DankFlumeMister/StarShield/docs/decision-package-2026-09-18.md

# 待决策项决策包（2026-09-18）

> 本文件把 `docs/decisions.md`「待定」清单里的 **9 项**逐项推进到可决策状态：
> **现状 → 事实依据 → 选项 → 推荐 → 代价 → 待你拍板**。
> 已经能定案的项（P12、P15）已直接落地并同步到原理图与文档；其余项需要你确认后我再动手改。

## 0. 总览

| # | 项 | 类型 | 状态 | 我的推荐 | 需要你拍板 |
| --- | --- | --- | --- | --- | --- |
| 1 | **P12** `ZMK_RGB_UNDERGLOW_EXT_POWER` | 固件 | ✅ **已关闭** | —（早已开启） | 否 |
| 2 | **P15** `F1` 保险丝额定值 | 硬件 | ✅ **已定案并落地** | 2 A hold / 1812 PTC | 否（已知会你） |
| 3 | **G2** PCB 板框外扩量 | 结构 | ✅ **已确认（2026-09-18）** | 4 mm/边 ⇒ PCB 约 379 × 127 mm | 否 |
| 4 | **G3** 安装孔数量与位置 | 结构 | 🟡 部分可定 | 数量 **8 个 / M2** 已定；**坐标留到 B4** | 否（坐标在 B4 定） |
| 5 | **G4** 外壳分件方案 | 结构 | ✅ **用户自理（2026-09-18）** | 本项目只产出 3D 模型文件 | 否 |
| 6 | **G6** 定位板是否纳入第一版 | 结构 | ✅ **已确认（2026-09-18）** | **纳入** | 否 |
| 7 | **C4** 是否引入 ZMK Studio | 固件 | ✅ **已确认（2026-09-18）：暂不启用** | 物理布局已存在，将来启用只差两行配置 | 否 |
| 8 | **C6** 是否并行做树莓派 MIT 验证 | 固件 | ✅ **已确认（2026-09-18）：不做** | 成本太高；兼容性风险改由 C5 直接实测承接（建议先买 ESP32-S3 最小系统板） | 否 |
| 9 | **ZMK config 是否独立仓库** | 仓库 | ✅ **已确认（2026-09-18）** | **不拆** | 否 |

---

## 1. P12 —— `ZMK_RGB_UNDERGLOW_EXT_POWER` ✅ 已关闭（文档滞后，不是没做）

**现状**：`firmware/boards/shields/starshield/starshield.conf` **第 31 行已是**
`CONFIG_ZMK_RGB_UNDERGLOW_EXT_POWER=y`，其前置 `CONFIG_ZMK_EXT_POWER=y` 也在（第 47 行）。

**结论**：这一项**早已落地**，挂在待定清单里是文档没同步。语义正是我们想要的
（RGB 开关联动 `ext-power`，关灯时经 Q1/Q2 反相级**物理切断** LED 供电，见 ADR-0005）。
已在 `decisions.md` 标为已关闭。

---

## 2. P15 —— `F1` 保险丝额定值 ✅ 已定案：**2 A hold / 1812 自恢复保险丝**

### 事实依据（Bourns MF-MSMF 系列官方降额表，已核对）

`Ihold`（A）随环境温度的降额值：

| 型号 | 23 °C | 40 °C | 50 °C | 60 °C | 70 °C | 85 °C | Vmax |
| --- | --- | --- | --- | --- | --- | --- | --- |
| `MF-MSMF150/24X`（1.5 A 档） | 1.50 | 1.25 | 1.13 | **1.00** | **0.88** | 0.69 | 24 V |
| **`MF-MSMF200`（2 A 档）** | 2.00 | 1.80 | 1.60 | **1.50** | 1.40 | **1.25** | 8 V |

工作电流：**≈1.0 A**（ILIM 档 `K_ILIM / R_ILIM = 1610 / 1600`，且输入限流**已含系统负载**，
所以正常工作中保险丝永远不会看到更大电流）。

### 判据①（最高环境温度下不误断）—— **1.5 A 档不合格**

- 1.5 A 档在 **60 °C 时 Ihold = 1.00 A，恰好等于工作电流 ⇒ 零余量**；70 °C 时 0.88 A ⇒ **会误断**。
- 键盘是**密闭 3D 打印壳**，且 BQ24072 在 1.0 A 时耗散 **1.3 W**（`Tj ≈ 83 °C`）
  ⇒ 板内 50–60 °C **完全可能**，不是极端假设。
- 2 A 档在 60 °C 仍 **1.50 A**（余量 50%），85 °C 时 1.25 A（余量 25%）⇒ 通过。

### 判据②（压降不影响充电）—— 通过

`MF-MSMF200`：`Rmin = 20 mΩ`、`R1max = 80 mΩ` ⇒ 1.0 A 下压降 **20 mV（常态）/ 80 mV（最坏）**。
BQ24072 的 `VIN-DPM` 阈值 = **4.35 / 4.5 / 4.63 V（min/typ/max）**。
5 V 输入减去最坏 80 mV ⇒ **≥4.92 V，余量 ≥0.29 V** ⇒ 不会触发降流。✅

### 已执行

- `docs/_tools/power_design.py`：`F1` value `1.5A` → **`2A`**；
  封装 `Fuse_0603_1608Metric` → **`Fuse_1812_4532Metric`**（已核实 KiCad 官方库存在，
  另有 `..._HandSolder` 变体）；补 `MPN` / `Note`；四处说明文字同步。
- 重跑 `gen_power_sch.py` + `verify_power.py`：**19 元件 / 70 条连接，ERC 0 error / 2 warning**（2 条为待 B2 接线的跨图标签）。
- 按位号 `F1` 全文 grep 后同步：`power-architecture.md`（§头、§3.1、§3.1 UNVERIFIED、§3.4、§3.7、§6 P13/P15）、
  `decisions.md`（P15、P13）。

### 代价（须知情）

1. **trip 电流由 3 A 升到 4 A** —— 保护能力略降。但输入过流本就由 BQ24072 的 ILIM 档负责，
   保险丝只挡**硬故障**（焊接桥接、输入电容击穿、座子短路）。
2. **Vmax 由 24 V 降到 8 V** —— 对合规 5 V USB 足够；异常高压时保险丝先断开，反而保护后级
   （`IN` 脚绝对最大额定 26 V，不会先坏）。
3. **封装 0603 → 1812**（4.55 × 3.24 mm）—— 占板面积约 11 倍；但**更好手焊**，
   不违背「被动件统一 0603」的本意（那条针对 R/C）。

### 类型为什么选自恢复（PTC）而不是一次性熔断丝

新手不会换件。一次性熔断丝跳了 = 板子「充电坏了」，对教程项目是灾难；
PTC 冷却自愈，故障表现为「拔线等一会儿就好」。

**残留**：LCSC 料号待 BOM 阶段补；若你要求 **≥16 V** 额定电压，需改选 2 A/16 V 的 1812 PTC（料号另行确认）。

---

## 3. G2 —— PCB 板框外扩量

**推荐：确认 4 mm/边**（键区 371.5 × 119.1 ⇒ PCB **约 379 × 127 mm**，与 `hardware-geometry.md` §1.1 既有估算一致）。

| 方案 | PCB 外框 | 外壳外沿 | 判定 |
| --- | --- | --- | --- |
| 3 mm/边 | 377.5 × 125.1 | 约 381.5 × 129.1 | 🟡 可行，但螺丝柱（φ4–5 mm）几乎贴住键区边缘 |
| **4 mm/边（推荐）** | **约 379 × 127** | **约 383 × 131** | ✅ 侧壁壁厚 2 mm + 螺丝柱仍有余量 |
| 5 mm/边 | 381.5 × 129.1 | 约 385.5 × 133.1 | 🟡 可行但外观更笨重；对打印床更不利（见 G4） |

**依据**：① 打印床 256 mm —— 379 mm 外壳按等分两件时每件约 190 mm，仍在床内；5 mm 方案每件约 193 mm，也还行。
② 3D 打印侧壁实用下限 2 mm + M2 自攻螺丝柱（柱心距板边 ≥2.5 mm）⇒ 板边到键区至少 3.5 mm。

⚠️ **依赖项**：外扩量必须与 nice!nano 的 USB-C 开孔（G7）协调 —— 其板载 USB-C 要能从侧壁够到，
该尺寸待 B6 量实物后定。**这条不定死，G2 的 4 mm 仍可能在 B6 后微调。**

---

## 4. G3 —— 安装孔数量与位置

**可定部分**：
- **数量 8 个**（与参考板 Apollo87H 实测一致）；379 mm 长的板靠 4 个角孔抗弯不够。
- **规格 M2 自攻 + 3D 打印底壳螺柱**（Apollo87H 用的是 Würth `9774035243R` 贴片螺柱，可作备选但需单独核实成本）。

**必须留到 B4 的部分 —— 坐标**：

1. 孔位必须落在**键位开孔之外**（不能压到任何 1u 单元）；
2. 必须避开 **G5 的两处电池仓**（左右两侧各 10.5 × 56 × 68 mm）；
3. 必须避开 nice!nano 排针（2×12，30.48 mm 长）下方与其 USB-C 的侧壁开孔区；
4. 板边到孔心留 ≥2.5 mm 铜皮余量；
5. 若 G6 采纳定位板，**定位板孔位必须与 PCB 同源生成**，不能各画一份。

⇒ 现在把坐标定死，会被 B4 的排针/电池仓/走线布局推翻。**建议现在只定「数量 + 规格 + 布孔原则」。**

---

## 5. G4 —— 外壳分件方案

> ✅ **用户定调（2026-09-18）：外壳分件 / 打印由用户自理，本项目只产出 3D 模型文件。**
> 下面的几何分析因此**不再是待决策项，而是给用户的客观事实输入**，保留如下。

**原方案（主键区一体 + 小键盘一体）不可行**，论证已写进 `hardware-geometry.md` §3.1：

| 部件 | 跨度 | 毫米 | + 双边留边 | 能否放进 256 mm 床 |
| --- | --- | --- | --- | --- |
| 小键盘 + 导航簇（**在左侧**） | 约 4u | 76.2 | 约 84 | ✅ |
| **主键区** | **15u** | **285.75** | **约 294** | ❌ **超床 38 mm** |

且**旋转 45° 摆放也救不回来**（294 × 130 mm 旋转后外接盒约 300 mm，仍 > 256）。

### 选项

| 方案 | 每件尺寸 | 缝数 | 主键区是否被切 | 评价 |
| --- | --- | --- | --- | --- |
| A. 主键区 + 小键盘 | 84 / **294** mm | 1 | 否 | ❌ **几何不可行** |
| **B. 等分两件（推荐）** | **各约 190 × 127** mm | 1 | **是** | ✅ 缝数最少；**刚度由整块 PCB 桥接** |
| C. 三件（小键盘 + 主键区两半） | 约 84 / 147 / 147 mm | 2 | 是 | 🟡 每件更小、更好打印，但多一道缝与装配工序 |

**推荐 B**（已被接受为「客观建议」；最终分件由用户自理）。关键理由：本项目 **PCB 本身就是上盖且是整块的**
（`decisions.md` §结构件），底壳接缝处的刚度与手感一致性**由 PCB 保证** ——
原方案「避免拦腰截断」的顾虑建立在「没有整块刚性件」的前提上，在本项目里不成立。

⚠️ 缝的位置须落在**键位列边界**上（不得切过任何开孔），并在 B4 与板框、电池仓一起定。

---

## 6. G6 —— 定位板是否纳入第一版

| 方案 | 优点 | 代价 |
| --- | --- | --- |
| **A. 纳入（推荐）** | ① **热插拔座的常规用法需要定位板** —— 插拔力与侧向力由定位板承担，而不是由焊点上的卡扣独扛；② 轴体对齐与键帽高低一致性好（新手最容易翻车的点）；③ 遮住 PCB 上盖，观感完整 | ① 多一份约 379 × 127 mm 的板（FR4，成本 待 BOM 核实）；② 开孔必须处理**异形阶梯 Enter**（i=52，用 `matrix.json` 的 `unionX_u/unionW_u`）；③ 总厚度增加 |
| B. 不做（PCB 上盖直露） | 少一份料、少一道工序；与「PCB 当上盖」字面一致 | ① 热插拔座独自承担插拔力 —— **无公开数据支持，标 ❓ UNVERIFIED**；② 轴体对齐完全靠热插拔座自身定位；③ 键帽高低一致性差 |

**推荐 A**，理由是本项目已决定用**热插拔座**，而热插拔座的成熟用法配套定位板。
⚠️ 若选 A，G3 的安装孔必须与定位板**同源生成**；
若选 B，需把「无定位板 + 热插拔座」的可靠性列为投板后实测项（目前无任何先例数据）。

---

## 7. C4 —— 是否引入 ZMK Studio

### ✅ 前提更正：物理布局**已经存在**，不是待办

`firmware/boards/shields/starshield/starshield_transform.dtsi` 里的 `physical_layout0`
**已带 95 条 `keys`**（centi-keyunit，含 `w`/`h`），由 `gen_transform.mjs` 从 `matrix.json` 派生。
文件头注释也写明「`keys` 属性是 ZMK Studio 支持所必需的」。

⇒ **Studio 最大的前置工作量已经做完了**。C4 现在只剩一个问题：**要不要启用 Studio 本体**。

### 事实依据

- ZMK Studio 提供**运行时改键位**（免重刷）。官方 2024-11-12 宣布 MVP GA。
- 启用方式（按官方文档）：build 加 `studio-rpc-usb-uart` snippet + `CONFIG_ZMK_STUDIO=y`。
  ⚠️ **机制随版本变化**：本机 `research/_clones/zmk`（main）里**没有**该 snippet 目录，
  取而代之的是 Kconfig `ZMK_STUDIO_TRANSPORT_UART`（由 `minivan_studio_tester` 选择）
  ⇒ **必须按我们钉住的 v0.3.0 实际核实**，不能照抄文档。
- Studio 构建会强制 `ZMK_BEHAVIORS_KEEP_ALL`（把所有 behavior 都编进去）⇒ 固件体积与编译时间上升。
- Studio 走 **USB** —— 本项目唯一的 USB 通道是 nice!nano 板载 USB-C（经底壳侧壁开孔），
  **可用**，但孔位还待 B6 量测（G7）。

### 选项

| 方案 | 内容 | 风险 |
| --- | --- | --- |
| **A. 暂不启用（推荐）** | 保持现状；物理布局已在，日后启用只差两行配置 | 无 |
| B. 现在启用 | `build.yaml` 加 snippet、`.conf` 加 `CONFIG_ZMK_STUDIO=y` | 中：依赖版本间不一致的 RPC 机制（需先实测 v0.3.0）；固件变大；教程多一层不确定依赖；且 USB 开孔位置还没量测 |
| C. 仅在文档里写「可选启用步骤」 | 不改构建，教程给出做法 | 低 |

**推荐 A + C**：收益（免重刷改键位）对新手教程确实有吸引力，但启用时机不利 ——
① 机制在 v0.3.0 与 main 之间不一致，需先实测；② USB 通道还依赖一个**未量测的开孔**。
⇒ 建议**等 B2 完成、G7 量测之后**再单独评估；届时只是两行配置的事，物理布局无需再动。

---

## 8. C6 —— 是否并行用树莓派 MIT 方案先验证 Dongle 链路

**背景**（ADR-0011）：小尺寸 Dongle 的开源实现**许可证全部不可用**（Nordic-5-Clause 或未声明），
可合法复用的 MIT 方案只有树莓派系：

| 项目 | ★ | 许可 | 平台 |
| --- | --- | --- | --- |
| `bahaaador/bluetooth-usb-peripheral-relay` | **334** | MIT | 树莓派 Zero 2 W（Go） |
| `quaxalber/bluetooth_2_usb` | 89 | MIT | 树莓派（Python） |

### 它能验证什么、不能验证什么

- ✅ **能验证**：「ZMK 键盘 ↔ 通用 BLE HID 主机」这一环。这正是 ADR-0011 未核实清单里
  风险最大的一条 —— `esp_hidh` 的官方示例是对着自家 `esp_hid_device` 调的，**对真实 ZMK 键盘未验证**。
- ❌ **不能替代**：ESP32-S3 固件开发本身（那块工作量不会因此减少）。
- ⚠️ **自身也有未验证点**：该项目 README 只写 *"Bluetooth keyboards and mice"*，
  **未明确提 BLE / HOGP**，兼容性属推断。

### 推荐：**做，但不占关键路径**

- 若手上有树莓派（或愿意花约 ¥150 采购 Zero 2 W + 配件）⇒ 在 B2/B4 推进的同时并行跑一次，
  把「ZMK ↔ BLE HID 主机」这个最大不确定性提前消掉。
- 若需专门采购且不想等 ⇒ 降级为**投板后的验证步骤**，不阻塞当前主线。
- ⚠️ 无论哪种，它**不解锁** C5（ESP32-S3 固件）的任何工作量。

---

## 9. ZMK config 是否独立仓库

**事实依据**：ZMK 官方把「用户配置」与「固件核心」分离为**推荐做法**
（独立 `zmk-config` 仓库：无需本地工具链、核心更新不冲突、配置单独版本管理）；
而**键盘硬件本身**应以 **ZMK module** 形态分发（`zephyr/module.yml` + `boards/shields/` + `*.zmk.yml` 元数据）。

**本仓库现状**：`firmware/` 里既有 shield 定义（`boards/shields/starshield/`，含 `starshield.zmk.yml` 元数据）
也有 `build.yaml` / `west.yml` / keymap ⇒ **既是 module 的形，又是 config 的形**，但没有 `zephyr/module.yml`。

### 选项

| 方案 | 优点 | 代价 |
| --- | --- | --- |
| **A. 保持单仓库（推荐）** | ① CI 已跑通，不动就不冒风险；② 新手教程只需一次 `git clone`；③ 许可证链与「一块板一个仓库」的直觉一致；④ 键位改动集中在 `firmware/` 一处 | 用户改键位需 fork 整个硬件仓（ZMK 生态里很常见） |
| B. 拆成硬件仓 + config 仓 | 符合官方「用户 config 独立」的推荐；用户 fork 的仓很小 | 两个仓要维护；`west.yml` 要指向自己的 remote；CI 要复制一份；教程要解释两个仓的关系 |
| C. 单仓库 + 补 `zephyr/module.yml` | 两种用法都支持（直接用本仓构建 / 当 module 引入别人的 config） | 需重排目录（module 根目前是 `firmware/`，而 `west.yml` 写的是 `self: path: config` —— 两者语义冲突，须实测验证） |

**推荐 A**。C 想法好但**存在结构冲突未解决**（module 根 vs west self path），
在有人真的要求「以 module 方式引入」之前，不值得为此改动已跑通的 CI。

---

## 10. 顺带发现的一处文档冲突（非待决策项，但需修）

`docs/decisions.md` §硬件 写「**Dongle 用 Seeed XIAO nRF52840**」，
但与 **ADR-0011** 和 `PROJECT_HANDOFF.md` §3 的「**ESP32-S3 + ESP-IDF 官方示例**」冲突
（前者是 ADR-0011 之前的旧值，未同步）。`firmware/build.yaml` 的注释里也还留着 XIAO 的痕迹。
⇒ 建议下次改固件文档时一并清理（本次未动，以免与本轮决策混在一起）。

### 10.1 另一处易踩的编号陷阱（非冲突，但值得写进文档）

- `docs/_generated/matrix.json` 里的 `index` 是 **1 起**：`index 3 = Num Lock`、`index 52 = Enter`。
- keymap / transform 里的**位置号是 0 起**：`位置 2 = Num Lock`、`位置 51 = Enter`。
- ⇒ **同一个「Enter」在两处相差 1**。`hardware-geometry.md` §1.4.1 写的是
  `matrix.json` 的 `index=52`，而 `starshield_transform.dtsi` 的注释写的是 `51 Enter`。
  两者都对，但混用会差一位 —— **已在 `hardware-geometry.md` §1.4.1 补注说明**
  （2026-09-18）。已核实：两条链一致，不是 bug。

### 10.2 🔴 `hardware-geometry.md` §1.4 大键位尺寸表的错误（已修正）

用户问「§1.4 里为什么有两个小键盘 Enter，尺寸还不一样」⇒ 追查后确认**是文档错误**，已按 KLE 权威源修正：

| 项 | 旧表（错） | 实际（KLE 权威值） |
| --- | --- | --- |
| 小键盘 Enter | 写了**两行**：`1.5u × 2u` 和 `1u × 2u`（标「Enter(左侧)」） | **只有一颗，1u × 2u**（KLE：`{"x":0.25,"h":2}`，无 `w` ⇒ 宽取默认 1u） |
| 小键盘 `+` | `2u` | **1u**（KLE 里 `/ * - +` 四颗都无 `w`，均为 1u × 1u） |

**错误成因**：① 「1.5u 宽」是把**主键区** Enter 的上半段宽度误套到了小键盘 Enter 上；
② 「Enter(左侧)」是对同一颗键的重复计数（小键盘本来就在板的左侧）。

**交叉印证**：`docs/matrix-assignment.md` 的「2u 高键」清单一直是
「小键盘 `Delete`、小键盘 `Enter`、主键区 `Enter`」三颗，与本表旧版不一致 —— 即旧表是孤例。
`docs/_generated/matrix.json`（生成链派生）与 KLE 一致：全库 Enter 标签只有 2 个
（主键区 i=52、小键盘 i=68），后者 `w_u=1, h_u=2`。
