DankFlumeMister/StarShield/docs/adr/0002-onboard-bq24072-charger.md

# 在主 PCB 上集成充电电路（BQ24072），而非依赖控制器模块

nice!nano v2 最高 500mA 充电，SuperMini 克隆板仅 100–300mA，两者都限制可用电池容量，且都没有电源路径管理——插着 USB 时电池仍在充放电循环。

我们把 BQ24072 充电 IC 直接做在主 PCB 上。它支持最高 1.5A 充电，并带 DPPM 电源路径管理，插 USB 时键盘直接由 USB 供电。

## Consequences

3000mAh 电池约 1.5–2 小时充满；插 USB 时不消耗电池；电池容量完全自由。代价是 PCB 上多一颗 QFN-16 芯片及外围元件；控制器模块的板载充电器闲置不用。

> ⚠️ **勘误（2026-09-17，不改写原决策）**：电池容量已改为 **2×5000 mAh 并联（10000 mAh）**。
> 上述「1.5–2 小时充满」的估算随即作废 —— 本项目 **2026-09-18 定稿为 ILIM 档、ICHG ≈1.0 A**
> （`R_ISET` = 887 Ω），充满 10 Ah 约 **10 h**。⚠️ 该电流**超出** 5.1 kΩ CC 下拉所声明的 500 mA，
> 是**有意的取舍**（依据：商用同容量键盘的实测充电区间 0.035–0.163C），见
> `docs/power-architecture.md` §3.7。且因 10 h 仍压在安全定时器 9.6–12 h 的边缘，
> **`TMR` 已改为接 `VSS` 禁用定时器**。另：「支持最高 1.5A 充电」是**芯片编程上限**，
> 不是本板可稳定取得的电流。**本 ADR 的核心决策（自建充电器 + 电源路径管理）不变。**

## 修订（2026-09）：明确**保持 `BQ24072`**，不换 `BQ24075`

在 P7（电池断电方案）的调研中曾考虑换用 **`BQ24075`**（与 `BQ24072` **封装完全相同**，
pin 15 由 `TD` 变为 `SYSOFF`，可 drop-in），以便用一个小开关切 `SYSOFF` 实现电池断电。

**该方案最终未被采用**：用户决定**走成熟路线，不设电池断电开关**
（关机 = 拨到有线档 + 拔线）；见 **ADR-0010**。

⇒ **本 ADR 的核心决策不变，且 `BQ24072` 保持原样**：

- 不需要 `SYSOFF` ⇒ **不换 `BQ24075`**
- 不需要「插 USB 强制拉低 `SYSOFF`」⇒ **不需要那颗 `2N7002`**
- `BQ24072` 的 `~{CE}`（pin 4）与 `EN1/EN2` 限流配置按原计划处理
- ⚠️ **`BQ24072` 没有 `SYSOFF`，无法用芯片断开电池** —— 这是已知且已接受的取舍

其余取值不变，详见 `docs/bq24072-pinout.md` §3。
