DankFlumeMister/StarShield/docs/adr/0006-change-to-95-key-layout.md

# 形态从 87 键 TKL 变更为 95 键紧凑全尺寸

项目早期确定形态为 87 键（TKL）单体键盘，并以 Apollo87H 作为物理布局参考基线。

用户随后提供了自己的初版布局（`sketch/keyboard-layout.json`，KLE 格式），经核实为 **95 键**：在 TKL 基础上增加了**独立小键盘**（`/ * - + 7 8 9 4 5 6 1 2 3 0 . Del`）与**导航键簇**（`Ins Home PgUp End ↓ PgDn ← ↑ →`）。用户确认这就是 StarShield 的最终形态。

我们决定采用该 95 键布局作为项目形态。

## Considered Options

- 维持 87 键 TKL：与用户实际布局不符。
- 改用 96 键 1800 紧凑布局：与 95 键接近但键位不同，用户已给出明确布局。

## Consequences

- 矩阵规模增大（需覆盖小键盘区），行列分配需重新规划。
- PCB 与外壳尺寸增大，256mm 打印床下分件需求更明确。
- **Apollo87H 参考基线部分失效**：它是 87 键 TKL、无小键盘，仅能覆盖主键区；小键盘与导航区的布局需另行设计。
- Per-key RGB 灯珠数从 87 增至 95，待机漏电估算相应上调。
- 项目此前所有"87 键"表述需同步更正。
