DankFlumeMister/StarShield/docs/adr/0007-rgb-powered-directly-from-battery.md

# RGB LED 由电池直供，不加 5V 升压电路

第一版 RGB（95 颗 `SK6812MINI-E`）的供电方式需要在两种方案间选择：
电池直供（3.0–4.2 V），或加一颗 5V 升压 IC 后供电。

参考基线 Apollo87H 的做法**不能直接照搬**：实测其 87 颗 LED 的供电引脚全部接在 `5V` 网络上，
而该板是**纯 USB 供电**，5V 直接来自 USB-C VBUS。StarShield 是电池供电，
5V 需要额外升压才能得到。

我们决定：**第一版 LED 直接由电池供电（`VLED` 接电池/`OUT` 轨），不加升压电路。**

## 依据

本项目选用的 `SK6812MINI-E`（LCSC C5149201）标称**工作电压 3.7 V ~ 5.5 V**，
而 LiPo 电池的常规工作区间为 3.7–4.2 V，**落在规格范围内**。

> ⚠️ 该电压范围来自分销商商品参数表，非原厂 datasheet PDF（本环境无法抓取 PDF）。

## Considered Options

- **加 5V 升压 IC**：全电压区间亮度与颜色稳定；但增加一颗 IC、一个电感、若干电容，
  且**升压 IC 自身的静态电流（通常几十 µA 起）会直接侵蚀无线键盘的待机续航**
  （目标待机电流仅约 20 µA）。与 ADR-0001/0005 的省电目标直接冲突。
- **改用 5V 专用的其它灯珠**：不解决供电问题，只是把问题留在原地。
- **电池直供**：零额外元件、零额外静态电流；代价是电池低于 3.7 V 后 LED 略低于标称电压。

## Consequences

**收益**：省掉升压电路（成本、面积、静态电流），保住无线续航目标。

**代价与风险**：
- ⚠️ 电池放电到 3.7 V 以下时，LED 已低于标称工作电压，**亮度会下降、颜色可能偏移**。
  LiPo 在 3.4–3.7 V 区间仍有可观容量，所以这是**实打实会遇到的**情况，不是理论边界。
- 缓解手段（固件层，无硬件成本）：低电量时下调 RGB 亮度上限。第一版建议配合采用。

## 待跟进

- ⚠️ **峰值电流约束**：12 mA/通道 × 3 通道 × 95 颗 ≈ **3.4 A**（100% 灰阶），
  按厂家建议的 70% 灰阶约 **2.4 A**。这**超过 JST-PH 2.0 连接器的 2 A 额定**。
  需在 PCB 阶段决定：限制固件最大亮度、或改用更大电流的连接方式。
  详见 `docs/power-architecture.md` 第 5 节。
- ⚠️ LED **静态电流实测 0.6 mA/颗 × 95 ≈ 57 mA**，印证 ADR-0005 的电源门控是必需的；
  建议据此修正 ADR-0005 中「约 95 mA」的估计值。
- 若后续需要全电压区间稳定亮度，再评估升压方案，但必须选**低静态电流 + 带使能脚**的型号。
