DankFlumeMister/StarShield/research/power-trace-width-precedent.md

# 电源走线宽度：商业键盘 / 社区开源方案对标

**调研日期**：2026-09-20
**触发**：投板前开口项 —— 本板 VBUS 受几何限制只做到 0.2–0.3 mm（1.0 A 充电），
且 `.kicad_pro` 的网络类未生效，需判断「要不要加宽 + 要不要真挂网络类」。

**来源等级**

| 标记 | 含义 |
| --- | --- |
| **[SRC]** | 直接读取仓库源文件（原理图注释 / 板文件几何 / 阻值） |
| **[DOC]** | 官方规格书、厂家官方页面、既有拆解实证 |
| **[REPORTED]** | 第三方转述 |
| **[INFERENCE]** | 本报告推算 —— 已写出推断链 |

> **可比性提示（必读）**：走线宽度的绝对值**没有可比性**，因为各样本的充电电流相差
> 一个数量级（0.1 A ~ 1.4 A）。本报告一律归一化为 **mm/A（每安培配多少毫米线宽）**，
> 并用 IPC-2221 反算温升作为统一标尺。

---

## 0. 勘误与后续（2026-09-20 补充，务必先读）

### 0.1 🔴 勘误：本报告初版漏掉了本板最严重的一处（VCHG_IN）

初版第 1 节写「VCHG_IN 无走线（纯铺铜或仅焊盘）」——**这是错的**，成因是**我自己的量测脚本
用「精确网名」匹配，而该网的真实名字是** `电源 {slash} 充电 {slash} RGB 门控/VCHG_IN`
（带层级前缀）⇒ 匹配失败 ⇒ **静默漏报**（不是「真的没有」，是「没查到」）。

用规范化网名（取最后一个 `/` 之后的部分）重量后的事实：

| 网络 | 段数 | 总长 | 线宽 | 层 |
| --- | --- | --- | --- | --- |
| **VCHG_IN**（USB→F1→充电 IC 的**充电路径**） | 10 | **241.4 mm** | **全部 0.200 mm** | F.Cu / **In1 / In2（内层为主）** |

IPC-2221：0.2 mm **内层** 1 oz 载 0.97 A（ILIM 1550/1600）⇒ **ΔT ≈ 88 ℃**。
**这比 VBUS（26 mm @0.3 mm）和 VBAT/OUT 都严重**，是本次调研真正的头号问题。
⇒ 教训与 handoff §10.2 第 30 条同源：**匹配口径错了，结果会「看起来合理」地错**；
凡「某网络没有走线」这类结论，必须换一种匹配方式复核一遍。

### 0.2 本轮已按结论落地的改动（全部经 DRC 与七项校验器验证）

| 改动 | 内容 | 效果 |
| --- | --- | --- |
| **层叠** | 板文件显式写入 `(stackup)`，外层 0.035（1 oz）、**内层 0.0152（≈0.5 oz，JLC 默认）**；同步写进 `gen_pcb.py` | 铜厚不再只存在于厂家默认里。**初版曾声明内层 1 oz，后经 §0.5 瓶颈分析改为 0.5 oz** —— 0.5 oz 已够，且与实际下单一致、不必要求特殊选项 |
| **VBAT 铺铜** | In2，**一块 L 形**：x 40–350 / y 7.3–11.9 条带 + x 118–350 / y 11.9–27 主块（priority 1） | 覆盖 3 条最长走线（122 / 57 / 56 mm）；沿途最窄铜高 **3.10 mm** |
| **OUT 铺铜** | In1，x 262–330 / y 5–22 | +753 mm²；**避开 x<262** 以保 U1 散热焊盘在 In1 的 GND 花焊盘（首版 x=240 触发 `starved_thermal`） |
| **VCHG_IN 铺铜** | In2，x 45–262 / y 4.8–7.6 | +585 mm²，正好覆盖那条 208 mm 的 0.2 mm 充电路径 |
| **走线加宽** | VBAT/OUT：33 段（0.5→0.6/0.8/1.0/1.2/1.5 mm，逐段间距预检自动降档）；VCHG_IN：9/10 段 →1.0 mm | 长段（122/57/56/208 mm）**几何上夹死、加不宽** ⇒ 只能靠铺铜 |
| **网络类** | `Power` 类线宽 0.5→**0.25 mm**、过孔 0.8/0.4→0.6/0.3；模式表改为 `VBAT/OUT→Power`、`VLED→VLED`；删除原有的 `GND→Power`、`+3V3→Power` | 见 §0.3 |
| **自定义规则** | 新增 `hardware/pcb/StarShield/Starshield.kicad_dru`：Power 类走线 ≥0.25 mm | 见 §0.3 |

### 0.3 两个反直觉的实测结论（都已在本板复现）

1. 🔴 **KiCad 内置的 `track_width` 检查不按网络类生效。**
   把它按类改动毫无反应：`Power` 类线宽 0.25→0.5 时违规数**纹丝不动**；
   把**板级** `min_track_width` 0.127→0.4 时立刻冒出 199 条。
   ⇒ 想按类约束线宽，**只能用自定义规则**（`.kicad_dru`）。这一条把「挂上网络类就能让 DRC 查」
   的原计划推翻了 —— 网络类本身不是护栏。
2. 🔴 **本板工程里预置的 `netclass_patterns` 把 GND 也划进了 Power 类**
   （`VBUS/VBAT/GND/+3V3 → Power`，B4 版就有）。自定义规则一开，就标出 199 条 GND 的
   0.2 mm 缝合走线 —— GND 是平面网，线宽不是它的载流手段，属纯噪音。已把 GND 移出。

### 0.4 修订后的优先级（原报告第 4 节结论随之更新）

| 优先级 | 项 | 状态 |
| --- | --- | --- |
| 1 | **VCHG_IN 241 mm @0.2 mm**（充电路径，ΔT≈88 ℃） | ✅ 已加 585 mm² 铺铜 + 9 段加宽到 1.0 mm；余 1 段几何夹死（见下） |
| 2 | **VBAT / OUT**（灯轨电流，峰值 2.4 A） | ✅ 已加 2 179 mm² 铺铜 + 33 段加宽 |
| 3 | **层叠未声明** | ✅ 已写入（内外 1 oz） |
| 4 | 网络类/规则 | ✅ 已挂 `Power` 类 + 自定义规则（内置检查不认网络类，故必须配规则） |
| 5 | VBUS 0.2–0.3 mm | ⬜ **维持现状**（0.97 A 下 ΔT≈10–20 ℃，社区同电流段亦如此） |

**唯一保留的 DRC 命中项（已用「限额豁免」登记，超 1 条即失败）**：
VCHG_IN 那条 208 mm 的 0.2 mm 走廊 —— 两侧被邻近走线夹死（试算 0.3 mm 即撞线），
载流改由同网络铺铜承担。

### 0.5 瓶颈分析：铺铜到底够不够 2.4 A（决定层叠要不要强制 1 oz）

「加了铺铜」不等于「够用」——必须量**沿途最窄处**。做法：沿电流方向每 2 mm 取一个
x 截面，在该截面上以 0.05 mm 步长采样，统计**该网络自己的铜**（铺铜填充 + 走线 + 焊盘）
在 y 向覆盖的总高度，取路径上的最小值：

| 路径 | 内层铜高（最窄处） | **0.5 oz 载流 @ΔT20** | 1 oz 载流 @ΔT20 | 需求 |
| --- | --- | --- | --- | --- |
| **VBAT**（J2 → 充电 IC，In2） | **3.10 mm**（x≈270） | **2.22 A** | 3.66 A | 护栏 1.0 A / 绝对峰值 2.4 A |
| **VCHG_IN**（F1 → 充电 IC，In2） | **1.95 mm**（x≈110） | **1.59 A** | 2.62 A | 0.97 A |
| OUT（充电 IC → Q1，In1） | 0.75 mm | 0.80 A | 1.32 A | 与 F.Cu 2.76 A / In2 0.98 A 并联 |

沿途中位铜高：VBAT 3.5–6.2 mm（x 300 处 17.9 mm）、VCHG_IN 2.60 mm。

**结论：0.5 oz 内层就已满足**（VBAT 覆盖护栏 222%、绝对峰值 93%；VCHG_IN 163%）。

⇒ **因此把层叠声明从「内层 1 oz」改为「内层 0.0152 mm（≈0.5 oz，JLC 默认 / Conejo 同款）」**，
理由：① 与实际下单一致，**不必再要求用户记住特殊选项**；② 更保守；③ 不加成本。
若能指定内层 1 oz，灯轨峰值余量再 ×1.65（93% → 150%）—— 属可选加保险，非必需。

> 方法论提醒：本节的「铜高」是**该层截面上的覆盖量**，横向并联的层（如 OUT 的 F.Cu / In1 / In2）
> 未相加，故上表是**逐层保守下界**；真实能力只会更高。

### 0.6 同一轮里修掉的两个自身缺陷

1. **VBAT 左段铺铜没盖住走线**：上一版把带子放在 y 8.0–9.7，而左段走线在 y≈7.46–8.72
   ⇒ x≈108–126 处只有 0.3–0.5 mm 走线在承流（瓶颈分析查出来的）。
   已改为**一块 L 形单块**（x 40–350 的 y 7.3–11.9 条带 + x 118–350 的 y 11.9–27 主块）。
2. **两块 VBAT 铺铜互相重叠** ⇒ DRC 报 `zones_intersect`。合并成单块后消失。
   ⇒ 教训：**同层同网的多块铺铜也会被判重叠**，要合成就得用**非凸单多边形**。

---

## 1. 结论速览

> ⚠️ **本节是初版结论，已被 §0 修订**：初版漏掉了 VCHG_IN（充电路径 241 mm @0.2 mm，
> 最严重）；且「挂网络类就能让 DRC 查」的假设被实测推翻（内置检查不认网络类）。
> **看优先级请直接看 §0.4。**

1. ⭐ **VBUS 0.2–0.3 mm 不是问题，不必为此重布。**
   IPC-2221：0.3 mm / 1 oz 外层 ⇒ **1.00 A @ΔT10℃、1.36 A @ΔT20℃**；本板实际
   **0.97 A**（ILIM = 1550 / 1600 Ω）⇒ 温升约 **10℃**、26 mm 全长压降约 **45 mV**。
   社区同电流段的 osprey（ILIM 1.03 A）**也用 0.300 mm**。
2. ⭐ **真正需要看的是 VBAT / OUT，不是 VBUS —— 灯轨电流的瓶颈在那儿。**
   灯轨路径是「电池 J2 → VBAT → BQ24072(BAT→OUT) → OUT → Q1(PMOS) → VLED 平面」，
   其中 **VBAT 实测 341 mm 里约 317 mm（93%）走内层、宽 0.5 mm**。
   若内层铜是厂家默认的 **0.5 oz**，0.5 mm 内层走线只能载 **0.44 A @ΔT10 / 0.59 A @ΔT20**，
   而灯轨峰值 2.4 A（固件护栏 BRT_MAX=30 下约 1.0 A）。
3. ⭐ **社区「定义了网络类」但几乎从不分配**：抽查 137 份 `.kicad_pro`，
   33 份定义了 Power / PWR 类，**只有 2 份真的把网挂上去**。
   ⇒ 挂网络类不是追赶惯例，而是**让 DRC 真正能查**；想查就得自己挂。
4. ⚠️ **本板没有声明层叠（stackup）** ⇒ 内层铜厚取决于厂家默认。
   嘉立创官方叠层页写 4 层板内层 **0.0152 mm（≈0.5 oz）**、外层 1 oz。
   这一项不落盘，DRC 永远查不出来。
5. **商业侧存在结构性数据缺失**：商业键盘的 PCB 走线宽度没有可量化的公开数据
   （拆解照片无法定量测量）。可用约束只有「商用产品按 350–1400 mA 设计充电路径」
   （既有报告 [DOC]），且它们普遍是 2 层 1 oz + 铺铜。

---

## 2. 样本表（含归一化列与来源等级）

| 样本 | 层 | 电源网络 | 线宽 | 设计电流 | **mm/A** | 来源 |
| --- | --- | --- | --- | --- | --- | --- |
| **本项目** | 4 | VBUS（F.Cu） | 0.300（22.4 mm）+ 0.200（3.7 mm 颈缩） | **0.97 A**（ILIM 1550/1600） | **0.31** | [SRC] 板几何 + 阻值 |
| **本项目** | 4 | VBAT（93% 内层） | 0.500 | 灯轨峰值 2.4 A / 护栏 1.0 A | 0.21 | [SRC] 板几何 |
| osprey | 2 | VBUS | 0.300 | **≤0.475 A**（原理图注释 EN1=1,EN2=0）；ILIM 上限 1.03 A | **0.63 / 0.29** | [SRC] 原理图逐条注释 |
| Pancake_v8 | 2 | VBUS | 0.260（仅 6.8 mm，带铺铜） | 0.228 A（ISET 3k9） | 1.14 | [SRC] 阻值 + 板几何 |
| Conejo（我们照抄其门控） | **4** | VBUS / +5V | 0.305 / 0.254 | ISET = `RSET`（原理图未定值） | n/a | [SRC] 板几何 |
| nrfmicro | 2 | VBUS / VBAT | 0.200 | TP4054，**0.1–0.5 A** | 0.40–2.00 | [SRC]+[DOC] |
| piantor | 2 | VBUS / VCC | 0.400 | 小电流分体板 | n/a | [SRC] |
| crkbd（Corne） | 2 | VBUS | **0.508** | 无板载充电 IC | n/a | [SRC] |
| **Apollo87H**（本项目的参考板） | 2 | VBUS / 5V | **0.500** / 0.500 | 电流未知 | n/a | [SRC] |
| KLOR | 2 | VCC | 0.381 | 小电流 | n/a | [SRC] |
| Sweep / TOTEM / chitin | 2 | raw / vcc | 0.200–0.250 | 小电流分体板 | n/a | [SRC] |

**样本规模**：社区侧扫了本机 `research/` 下 **100 份去重后的 KiCad 板文件**
（按 文件名+大小 去重），137 份 `.kicad_pro`。

---

## 3. 推算与依据

### 3.1 本板实际电流 [SRC + INFERENCE]

- 充电电流：ISET = 890 / 887 Ω = **1.003 A**（K_ISET = 890 A·Ω，BQ24075 手册同款常数）
- 输入限流：ILIM = 1550 / 1600 Ω = **0.969 A**（K_ILIM = 1550 A·Ω，osprey 原理图注释佐证）
- ⇒ **VBUS 实际电流 ≈ 0.97 A**（输入限流封顶）

### 3.2 载流反算（IPC-2221）[INFERENCE]

公式 `I = k · ΔT^0.44 · A^0.725`，A 单位 mil²，k = 0.048（外层）/ 0.024（内层）。
常数出处：IPC-2221 曲线拟合值，多个在线计算器与标准解读站一致。

| 走线 | ΔT10 | ΔT20 | ΔT40 |
| --- | --- | --- | --- |
| 0.300 mm 外层 1 oz | **1.00 A** | 1.36 A | 1.84 A |
| 0.200 mm 外层 1 oz | 0.74 A | 1.01 A | 1.37 A |
| 0.500 mm 外层 1 oz | 1.45 A | 1.96 A | 2.66 A |
| 0.500 mm 内层 1 oz | 0.72 A | 0.98 A | 1.33 A |
| **0.500 mm 内层 0.5 oz** | **0.44 A** | **0.59 A** | 0.81 A |

目标电流所需宽度（ΔT=20℃）：

| 电流 | 外层 1 oz | 内层 1 oz | 内层 0.5 oz |
| --- | --- | --- | --- |
| 1.0 A | 0.20 mm | 0.51 mm | **1.03 mm** |
| 2.4 A | 0.66 mm | 1.72 mm | **3.43 mm** |
| 3.4 A | 1.07 mm | 2.77 mm | **5.55 mm** |

⇒ 2.4 A 这种量级**本来就不该用走线**，应该像 VLED 那样用整板铺铜（VLED 铺铜面积
56 658 mm²，[SRC]）。

### 3.3 灯轨路径的压降 [INFERENCE]

路径 `J2(332,10) → U1(BAT) → U1(OUT) → Q1(316,6)`，实测几何合计约 **145 mm 的 0.5 mm 走线**
（VBAT 约 70 mm + OUT 约 79 mm），大部分在内层：

| 电流 | 内层 0.5 oz | 内层 1 oz |
| --- | --- | --- |
| 1.0 A（固件护栏） | R=0.272 Ω，压降 **0.272 V**，0.27 W | 0.136 V，0.14 W |
| 2.4 A（灯轨峰值） | 压降 **0.653 V**，1.57 W | 0.326 V，0.78 W |

注：铜 ρ 取 1.7×10⁻⁸ Ω·m（25℃），未计 PMOS 导通压降与 BQ24072 内部 BAT→OUT 通路。

### 3.4 规范依据 [DOC]

TI BQ24072 数据手册 §12.1 Layout Guidelines 原文：
> 「The high current charge paths into IN pin and from the OUT pin **must be sized
> appropriately for the maximum charge current** in order to avoid voltage drops in these traces」

即 TI 给的是**定性要求**（按最大充电电流定尺寸、避免压降），没有给数值。
本板 VBUS 压降 45 mV，满足 TI 的判据；**VBAT/OUT 段 0.27 V 则明显偏离该判据**。

### 3.5 商业侧 [DOC] + 结构性缺失

既有报告 `large-battery-keyboard-charging-current.md` 已确认（官方手册口径）：
5000 mAh 以上键盘的充电电流实测区间 **350–1400 mA**（AULA L99 1300 mA、
Kzzi K98PRO 1400 mA、EPOMAKER TH87 ≤1 A）。⇒ 商业产品同样要为 ~1 A 的充电路径定尺寸。

**但商业键盘的 PCB 走线宽度无法量化获取**：公开资料只有拆解照片，不能测量线宽。
这是结构性缺失，不是没查到 —— 见第 5 节。

---

## 4. 对当前决策的意义

| 原判断 | 调研后 |
| --- | --- |
| 「VBUS 0.2–0.3 mm 偏窄，投板前要决定是否加宽」 | **不必加宽**。0.3 mm/1oz 外层在 0.97 A 下温升约 10℃、压降 45 mV，与社区同电流段（osprey 0.300 mm @1.03 A 限流）一致。若追求余量，可把 3.7 mm 的 0.2 mm 颈缩段补到 0.3 mm，代价极小 |
| 「网络类没挂上是待修回归」 | **结论不变但要改理由**：社区也几乎不挂（33/137 定义、2/137 分配）。挂上的**唯一价值是让 DRC 能查**，不是为了对齐惯例 |
| （原未列入） | 🔴 **新增最高优先级项**：VBAT / OUT 的 0.5 mm 内层走线承载灯轨电流，若内层铜为 0.5 oz 则严重偏窄（2.4 A 需 3.43 mm 或铺铜）；1 A 时也有 0.27 V 压降 |
| （原未列入） | ⚠️ **新增**：板文件未声明层叠 ⇒ 内层铜厚不可控，且 DRC 无法检查 |

**建议动作（按性价比）**
1. 在板文件里**显式声明层叠**（内外层铜厚），并按需向厂家指定内层 1 oz。
2. 把 VBAT / OUT 的关键段**移到外层并加宽**，或在内层改用铺铜（与 VLED 同层做法一致）。
3. 真正挂上 Power 网络类（VBUS / VBAT / OUT / VLED / VCHG_IN），让 DRC 的
   `track_width` 检查生效 —— 否则下次再犯同类错误仍然查不出来。
4. VBUS 的 0.2 mm 颈缩段可顺手补到 0.3 mm（可选）。

---

## 5. 诚实边界

- **样本性质**：社区样本是**便利样本**（本机 `research/` 里已克隆的仓库），不是普查；
  且以分体小键盘为主，与目标（95 键 + RGB + 10000 mAh）**不同构**，已用 mm/A 归一化但
  仍应尽量参考同电流段样本（osprey 1.03 A、Apollo87H）。
- **标称 vs 实测**：所有「设计电流」都是**由 ISET/ILIM 阻值反算的标称值**，不是实测电流。
- **推断 vs 读取**：线宽、层数、路径长度是**读取**；温升、压降、所需宽度是**推算**
  （IPC-2221 经验公式，1950 年代数据拟合，对现代叠层可能偏保守或偏乐观；
  IPC-2152 更精确但 IPC 已标注「不再维护」）。
- **铜厚不确定**：内层 0.5 oz 取自嘉立创官方叠层页 [DOC]；不同厂家/叠层不同，
  且本板未声明层叠 ⇒ 这是**需向厂家确认项**，不是已知事实。
- **结构性缺失**：商业键盘的走线宽度**拿不到可量化数据**（只有拆解照片）。
  任何「商业产品用 X mm」的说法都应视为不可得，勿据其下结论。
- **Apollo87H / crkbd 的电流未知**，故未做 mm/A 归一化，不能用来支持任何方向的结论。
