DankFlumeMister/StarShield/research/battery-charging-community-precedent.md

# 社区充电设计对照：BQ2407x 家族的实际接法

> ## 🔴 本报告的「对本项目结论」部分已于 2026-09-17 晚被容量变更推翻（阅读前必看）
>
> **触发**：电池容量由 **3000 mAh** 改为 **2×5000 mAh 并联（10000 mAh）**。
>
> **受影响的三条结论**（本报告正文仍保留原文，作为历史记录）：
>
> | 本报告的结论 | 变更后的实际情况 |
> | --- | --- |
> | `R_TMR` = 47 kΩ「本项目**必须装**」（§2.3 / §4 / §6 多处） | ❌ **已推翻**。10000 mAh 需约 **20.6 h** 充满，而定时器上限仅 **7.2–12 h** ⇒ 任何 `R_TMR` 都不够；现为 **`TMR` 直接接 VSS 禁用定时器**，`R_TMR` 已移除 |
> | 「本项目 0.5 A = 0.17C，是社区样本里 C 率最低的」（§3） | ⚠️ **数值失效**。10000 mAh 下 0.5 A = **0.05C**；且新增了「定时器」这堵墙（本报告写作时不存在） |
> | `R_ILIM` = 1.6 kΩ（§2.3 对照表） | ⏩ 曾改为 **1.5 kΩ**（对齐 osprey / designguide），**随后又改回 1.6 kΩ** —— 因 P13 定案切到 ILIM 档，1.6 kΩ 对应输入 ≈1.0 A；1.5 kΩ 时是 USB500 档下的「装了但不用」 |
> | 新增 `F1` = **500 mA** 保险丝（§5.1） | ⚠️ **位置仍成立，额定值已失效**。2026-09-18 输入档切到 1.0 A 后 500 mA 会**必然熔断** ⇒ 现为 **1.5 A** |
> | 全篇把「USB500 档 = 输入上限 500 mA」当作当前状态（§2 / §3 / §5.1） | ❌ **档位已变**。现为 **ILIM 档、输入 ≈1.0 A、充电 ≈1.0 A（0.10C）、充满约 10 h** —— 见 `docs/power-architecture.md` **§3.7**（该节同时修正了本报告引出的「建议维持 0.5 A」结论） |
>
> **本报告中仍然成立的部分**（不受容量影响）：
> - **输入限流档 4/4 全选 USB500、`EN1` 4/4 接 `OUT` 轨**（无一例接 `VBUS`）
> - **温度监测 3/4 禁用**；唯一实现者走「3 脚座 + 电芯自带 NTC」，**无任何样本用板上 NTC**
> - **`R_ISET` 要按 C 倍率换算、不能照抄绝对电流**（这条方法论不变，只是换算的基数变成 10000 mAh）
> - **Conejo 的保险丝位置不能照抄**（它在电池路径上）
> - **社区 ICHG 普遍 0.23 A**、主流做法是「不画充电电路、用控制器自带充电器」
>
> **后续调研（在售商用键盘）见 `research/keyboard-battery-capacity-precedent.md`** ——
> 那份报告才解释了「10000 mAh 该怎么做」，并给出了「消费级充电 IC 普遍无充电定时器」的
> 关键推断。⚠️ **开源样本 ≠ 行业实践**：本报告的 4 个 BQ2407x 样本都是小电池 DIY，
> 无法反映量产产品的形态决策。

**问题**：本项目的 `BQ24072` 充电子图里，输入限流档（USB500 vs ILIM）与电池温度监测（TS）
两项该怎么定？社区的真实工程是怎么做的？

**方法**：对本机 `research/repos/` 下 **31 个克隆的社区键盘硬件仓库**做两级扫描 ——
先扫全部 `.kicad_sch` 找出真正带**独立充电 IC** 的工程，再用项目自带的网表提取器
`research/kicadnet.py` 做**引脚级**连通性还原（`--list-parts` / `--comp` / `--net`）。

**证据标签**：
- **[NET]** —— 由 `research/kicadnet.py` 从 `.kicad_sch` 还原的网表（引脚级）
- **[FILE]** —— 直接读源文件（元件表 / 封装名 / 属性值）
- **[DS]** —— TI 数据手册 SLUS810N 原文（本地 PDF 抽取，见 `docs/bq24072-pinout.md`）
- **[INFERENCE]** —— 我的电路推断，明确不是文件读数
- **[UNVERIFIED]** —— 未能确认

> ⚠️ **提取器可信度声明**：`docs/PROJECT_HANDOFF.md` §10.2 第 10 条要求「引用网点结论前先交叉验证」。
> 本报告只采用**自洽**的结论（例如「TS 网络上恰有一颗电阻，其另一端在 GND」），
> 并对无法交叉验证的项**显式标为观察而非结论**。单点网络（只有一个引脚的网）一律不作为结论。

---

## 0. 先看清样本：社区主流根本不画充电电路

**[FILE]** 31 个仓库里，只有 **5 个**的原理图出现独立充电 IC：

| 仓库 | 充电 IC | 备注 |
| --- | --- | --- |
| `kurtis-lew/Conejo` | **BQ24075RGT** | 本项目的参考实现（ADR-0005） |
| `ebastler/osprey` | **BQ24075** | 与本项目同作者体系的成熟设计 |
| `Croktopus/zmk-designguide` | **BQ24075**（另有 TP4056 一路作对照） | 即 `ebastler/zmk-designguide` 的 2022 fork |
| `michaelrommel/nightliner` | **BQ24075RGT** | 唯一做了**真·电芯温测**的样本 |
| `joric/nrfmicro` | 自带（型号未逐一核对） | 无电池座，接模块 |

**其余 26 个没有独立充电 IC** —— 它们直接依赖控制器模块（nice!nano / 超迷你）**自带的充电器**。
⇒ **本项目「把 BQ24072 做在主 PCB 上」本身就是少数派做法**（理由是 ADR-0002 要电源路径管理）。
这也意味着：**这四个 BQ2407x 样本，就是这个问题上能拿到的最好证据集**，样本量小但针对性强。

---

## 1. 输入限流档：4/4 全部选 USB500，且 EN1 都接 **OUT 轨**

**[NET]** 四个 BQ2407x 工程的 `EN2` / `EN1` 接法**完全一致**：

| 项目 | EN2 | EN1 | 档位 | EN1 接到哪条轨 |
| --- | --- | --- | --- | --- |
| Conejo | `GND` | `VDDH` | 0/1 = **USB500** | VDDH（= `U1.10/11 OUT` 同网） |
| osprey | `GND`（网名 `EN2`） | `EN1` = 接 `+VSW` | 0/1 = **USB500** | +VSW（= `U2.10/11 OUT` 同网） |
| designguide | `GND` | `+VSW` | 0/1 = **USB500** | +VSW（= `U3.10/11 OUT` 同网） |
| nightliner | `GND` | `VIN` | 0/1 = **USB500** | VIN（= `U4.10/11 OUT` 同网） |

**三条独立结论：**

1. **没有一个项目用 ILIM 档**去换更快的充电速度 —— 全部接受 USB 的 500 mA 上限。
2. **`EN1` 一律接 `OUT` 轨，没有一例接 `VBUS`/`+5V`**。
   本项目独立推导出的同一条结论（理由：[DS] `EN1`/`CE` 等脚绝对最大额定仅 **7 V**，
   而 `IN` 可耐 26 V ⇒ 接 VBUS 遇到超压适配器会被打坏）在社区里得到 4/4 印证。
3. 两个项目都有一颗 `500mA` 保险丝（封装均为 `Fuse:Fuse_0603_1608Metric`），
   **但装在完全不同的位置** —— 这一点决定哪一颗可以照抄：

   | 项目 | `F1` 串在哪 | 判定 |
   | --- | --- | --- |
   | **nightliner** | **USB 输入侧**：`J1.A4/A9/B4/B9 (VBUS)` → `F1` → `FB1`（铁氧体磁珠）→ 充电器 `IN` | ✅ **正确位置**，与 USB500 档配套 |
   | **Conejo** | **电池路径**：`+BATT`（电池座 `J1.1`）→ `F1` → `VBAT`（`U1.2/3 BAT`） | ❌ **不可照抄**：串在电池路径上，**RGB 的全部放电电流都要流过它**（54 键全亮约 1.9 A）⇒ 必然误断 |

   **[NET] 依据**：Conejo `+BATT = {F1.2, J1.1, U2.2, U2.3, C5.1}`、
   `VBAT = {F1.1, U1.2, U1.3, R6.2, C6.1, C7.1}` —— 保险丝在电池座与充电器 `BAT` 脚之间；
   nightliner `F1.1` 与 USB-C 的四个 VBUS 焊盘同网、`F1.2` 与铁氧体 `FB1.1` 同网。

   ⇒ 若要照抄，**只照 nightliner 的位置（VBUS 侧）**。本项目已按此实现，见 §5。

> **[DS] 交叉校验**：TI 数据手册 §10.2 的官方典型应用反而用的是 `I_IN(MAX) = 1.3 A` /
> `I_FASTCHG = 800 mA`。也就是说 **TI 自己的参考设计比社区激进**，而社区一致选择更保守的 500 mA。
> 对本项目（新手教程、要「插上就能用」）来说，社区的选择更有参考价值。

---

## 2. 电池温度监测：3/4 禁用，1 个用**3 脚电池座**做真·电芯温测

**[NET] + [FILE]**

| 项目 | TS 接法 | 判定 |
| --- | --- | --- |
| **Conejo** | `U1.1 (TS)` → 网络 `TS` = {`R3.1`, `U1.1`}，`R3 = 10K`，`R3.2 → GND` | ❌ **禁用温测**（10 kΩ 到 GND） |
| **osprey** | `U2.1 (TS)` → 网络 = {`R5.1`, `U2.1`}，`R5 = 10 kOhm`，`R5.2 → EN2(=GND)` | ❌ **禁用温测**（10 kΩ 到 GND） |
| **designguide** | `U3.1 (TS)` → 网络 = {`R11.1`, `U3.1`}，`R11 = 10 kOhm`，`R11.2 → GND` | ❌ **禁用温测**（10 kΩ 到 GND） |
| **nightliner** | `U4.1 (TS)` → 网络 `BAT_TEMP` = {`J2.2`, `U4.1`}；`J2` = `Connector_JST:JST_XH_S3B-XH-A-1_1x03_P2.50mm_Horizontal` | ✅ **真·电芯温测**（3 脚电池座中间脚 = 电芯 NTC） |

**结论（本项目结论被印证）**：**3/4 用「一颗 10 kΩ 固定电阻到 GND」明确放弃温度监测** ——
这正是 `docs/power-architecture.md` §3.3 方案 A 的做法，也是 `[DS]` 数据手册认可的写法。

**唯一的反例 nightliner 走的正是 §3.3 方案 B，而且实现方式值得照抄**：
它把电池座换成 **3 脚 JST-XH（`S3B-XH-A-1`）**，中间脚命名为 `BAT_TEMP` 直接接 `TS` ——
也就是「**靠电芯自带的 NTC 引线，经连接器中间脚进芯片**」。

**[NET]** 旁证：nightliner 还画了一个「3 脚电芯模型」区块 —— `BT1`（+/− 两脚电池符号）
与 `TH1`（值为 `NTC`，2 脚）以及 `J4`（`JST_EH_B3B-EH-A_1x03`）——
其中 NTC 接在 **T 与 B− 之间**，正是真实带 NTC 软包电芯的内部结构
（3 脚 = B+ / T / B−，NTC 一端接 T、另一端接 B−）。

- ⚠️ **[UNVERIFIED]** `J4` 的中间脚（`N$13970_8509` = {`J4.2`, `TH1.2`}）**并未接到 `BAT_TEMP`**，
  而实体连接器走的是 `J2`。看起来 `J4 + BT1 + TH1` 是一个**建模/备用区块**而非实体路径。
  不作为结论。

### 2.1 没有先例支持「板上焊一颗 NTC」= 方案 C

**[FILE]** 严格扫描「真正的热敏元件 / 电池温度网络名」（排除 `ThermalVias` 这类误命中）后：
**31 个仓库里只有 2 个命中** —— `nightliner`（`TH1 NTC` / `BAT_TEMP`）与
`designguide`（`J5 Thermistor` 连接器 / 网络 `TEMP`）。

`docs/power-architecture.md` §3.3 方案 C（把 NTC 焊在 PCB 上测板温）在这些样本里
**没有任何先例**。**[DS] + [INFERENCE]** 数据手册原文也是
*"Connect the TS input to the NTC thermistor **in the battery pack**"* —— 明确指向电芯内部。

> 📌 **designguide 的 `J5` 值得单独记一笔**：它是一个标为 `Thermistor` 的 **2 脚 JST-PH**，
> `TEMP` 网络上挂着 `R15`/`R17`（各 `5 kOhm`）构成分压网络（**[NET]**）。
> **但 `TS` 引脚硬接 `R11 = 10 kΩ` 到 GND，`TEMP` 并未连到 `TS`**。
> ⇒ 也就是「**留了外接 NTC 的接口和分压网络，却没有接到芯片的 TS**」。
> **[UNVERIFIED]** 无法判断这是设计指南未完成、还是靠未画出的跳线选择 —— 不作结论。
> 但它说明：**「预留 NTC 接口」这件事在社区里是有人想到过的**，只是没走通。

---

## 3. 三个阻值取值的横向对照

**[NET] + [FILE]**（`R_ISET` / `R_ILIM` / `R_TMR`；换算用 `[DS]` 的 `K_ISET = 890 AΩ`、`K_ILIM = 1610 AΩ`）

| 项目 | `R_ISET` | ⇒ ICHG | `R_ILIM` | ⇒ 输入上限（若走 ILIM 档） | `R_TMR` | `TS` |
| --- | --- | --- | --- | --- | --- | --- |
| **Conejo** | `R2`，值写成 `RSET`（未填数字） | ❓未定稿 | 未见电阻 | — | `R1`，值写成 `RTMR`（未填数字） | 10 kΩ 禁用 |
| **osprey** | `R8 = 3.9 kΩ` | **≈0.23 A** | `R7 = 1.5 kΩ` | ≈1.07 A | `R6 = 47 kΩ` | 10 kΩ 禁用 |
| **designguide** | `R14 = 3.9 kΩ` | **≈0.23 A** | `R13 = 1.5 kΩ` | ≈1.07 A | `R12 = 47 kΩ` | 10 kΩ 禁用 |
| **nightliner** | `R5 = 3.9 kΩ` | **≈0.23 A** | ⚠️ 未见外接电阻 | — | ⚠️ 未见外接电阻 | 3 脚座真温测 |
| **本项目**（2026-09-17 状态） | `R4 = 1.78 kΩ` | **0.5 A** | `R3 = 1.5 kΩ` | ≈1.07 A | **`TMR` 接 VSS 禁用**（容量改 10000 mAh 后任何 `R_TMR` 都不够，见 `keyboard-battery-capacity-precedent.md`） | 10 kΩ 禁用 |

**⚠️ 一个会翻转结论的关键变量：电池容量差 6–15 倍**

上面这张表**如果不看电池容量就会读错**。**[FILE]** 三家的电池是：

| 项目 | 电池容量 | 出处 |
| --- | --- | --- |
| Conejo | **300 mAh** | 原理图图面文字 `"Battery (300mAh)"` |
| osprey | **200–250 mAh** | `readme.md` 与 `sheet_bmgmt.kicad_sch` 图面文字：`502030 (20x30x5 mm) → 250 mAh` |
| designguide | **readme 以 500 mAh 举例** | `readme.md`：*"0.5C and 1C (for a 500 mAh battery: 250 mA to 500 mA)"* |
| **本项目** | **3000 mAh** | — |

⇒ `R_ISET = 3.9 kΩ` 的真实含义是**按 C 倍率定的，不是按绝对电流定的**：

| 项目 | ICHG | 电池 | **C 倍率** |
| --- | --- | --- | --- |
| osprey | 0.23 A | 250 mAh | **0.91C**（几乎 1C 快充） |
| designguide | 0.23 A | 500 mAh | 0.46C |
| nightliner | 0.23 A | 未标注 | — |
| Conejo | 未填值 | 300 mAh | — |
| **本项目** | 0.50 A | 3000 mAh | **0.17C** |

⇒ **结论完全反转：社区根本不保守 —— 它们按 0.5–1C 在充**
（designguide 的 readme 把 *"0.5C and 1C"* 直接写成了惯例）。
**本项目的 0.5 A 是这套样本里 C 倍率最低的一档。**

**⇒ 所以「按社区成熟方案来」在 `R_ISET` 上的正确落地不是照抄 3.9 kΩ，而是按 C 倍率换算：**

- 社区意图区间 **0.5–1C** ⇒ 3000 mAh 对应 **1.5–3.0 A**
- 但两条硬墙挡在上面：芯片充电上限 **1.5 A**（`R_ISET` 最小 590 Ω）+ USB500 档输入上限 **500 mA**
- 本项目**维持 `R_ISET = 1.78 kΩ`（0.5 A）**：它已经是「USB500 输入档下能取到的满值」
  （输入 500 mA − 系统负载 ≈ 485 mA）。再往上必须切 ILIM 档，而社区 **4/4 都不用 ILIM 档**。
- ⚠️ 这是一个**明确的取舍，不是「和社区一致」**：本项目选择「USB 规范合规 + 低发热」，
  代价是 0.17C、约 6.2 h 充满。要靠近社区的 C 率，必须同时改输入档（见 §5 P13）。
**另两条（`R_ILIM` / `R_TMR`）：**

2. **`R_ILIM`：osprey 与 designguide 用 1.5 kΩ（≈1.07 A），本项目已对齐为 1.5 kΩ。**
   而且**三家都在 USB500 档下装着这颗电阻却不用它限流**，正是 `[DS]` 要求的
   「即使不用也必须装（悬空会关闭所有充电）」。本项目做法一致 ✅
3. **`R_TMR`：osprey / designguide 用 47 kΩ（≈6.25 h，与 `[DS]` 的 46.4 kΩ 示例一致）。**
   ⚠️ **本项目原先选的是「悬空用内部默认 5 h」，这次对照后改成了装 47 kΩ** —— 原因不是「社区这么做」，
   而是本项目自己的算术：ICHG 0.5 A 对 3000 mAh，**仅 CC 段就约 6.2 h > 内部默认 5 h**
   ⇒ 悬空会让安全定时器在充满前掐断（表现为「永远充不满、CHG 2 Hz 闪烁」）。
   0.23 A 的小电池样本反而用不到 6.25 h，两家装 47 kΩ 更像是照抄 `[DS]` 的典型应用取值；
   **对 3000 mAh 的我们，它是必需品。**
   > 📌 这条是本报告**修正了本项目既有结论**的唯一一条（原先 `power-architecture.md` §3.1
   > 用「定时器在 DPPM/热调节期间按比例变慢」论证悬空够用 —— 那个论证只在**节流发生时**成立，
   > 而正常 0.5 A 恒流段本来就是 6.2 h，与节流无关）。
   ⚠️ **nightliner 的 `TMR` 与 `ILIM` 在原理图原文里都是单点网络（无外接电阻）** ——
   **[FILE] 交叉验证**：其全部电阻值为 `1k/1k/1k/1k/3.9k/5.1k/5.1k/10k/806k/1M/2M`，
   没有任何落在 `1100–8000 Ω`（ILIM 允许范围）或 `18–72 kΩ`（TMR 允许范围）的元件，
   **与「未接」的提取结果一致**。⇒ 观察：该原理图未画这两颗电阻。
   `[DS]` 说 ILIM 悬空会关闭充电 ⇒ 这可能是原理图未完成而非量产状态。
   **本报告只记录观察，不判断该设计有缺陷。**

---

## 4. 顺带发现：社区做了、而我们还没做的七件事

这些不是「必须做」，但都是**有实物先例**的选项，列入备选清单。

| # | 做法 | 证据 | 对本项目的意义 |
| --- | --- | --- | --- |
| 1 | **USB 输入保险丝 500 mA**（Conejo `F1`、nightliner `F1`） | [FILE] 两家都用 `Fuse:Fuse_0603_1608Metric`，值 `500mA` | 🟡 便宜且与 USB500 档配套；本项目未做，值得考虑（也能挡住输入侧意外） |
| 2 | **输入 TVS**（nightliner `U2 = TVS2200DRV`） | [FILE] | 🟡 便携设备插劣质线时的保护 |
| 3 | **USB 数据线 ESD 保护**（nightliner `U3 = USBLC6-2SC6`） | [FILE] | 🟡 本版 D+/D- 未接，暂不需要；将来接数据线时应补 |
| 4 | **电量计 IC**：`MAX17048`（Conejo `U2`、osprey `U3`、designguide `U9`） | [FILE] 三家不约而同 | 🟢 **值得考虑**：本项目目前靠 nice!nano 的 ADC 估电量，精度差；但会增加 I²C 走线与 1 个器件 |
| 5 | **电池分压到 MCU ADC**（nightliner `R6 = 806k` / `R7 = 2M` → `VSENSE` → `U1.11 [L]_A7_P0.31`） | [NET] | 🟢 独立的电池电压检测通路，不依赖控制器内部；代价是一颗电阻 + 一个 ADC 脚 |
| 6 | **用固件控制充电电流/开关**（nightliner `R_ISET`（3.9 kΩ）的下端接 **MCU `P1.13`** 而非 GND，网络名 `CHARGE_CTRL_2`） | [NET] 网络 = {`R5.1`, `U1.4 [L]_P1.13`} | 🔴 **重要发现**：这是 §3.2 没列到的**第三条杠杆** —— 不管输入限流档怎么设，`ISET` 的下端由 GPIO 控制就能**开/关充电或改变充电电流**。⭐ 但 ⚠️ 代价是 ISET 上的电压会被 ADC 读作「实际充电电流」，接 GPIO 会让这个监测功能失效；且 `[DS]` 要求 ISET 上电短路检测，加 GPIO 引入未知 |
| 7 | **EP 散热焊盘带热过孔**（nightliner `U4` 封装 = `VQFN-16-1EP_3x3mm_P0.5mm_EP1.6x1.6mm_**ThermalVias**`） | [FILE] | ✅ 印证 `docs/bq24072-pinout.md` §2.2 的「EP 必须焊 + 配热过孔阵列」；本项目 B4 布局照做 |
| 8 | **物理电源开关**（nightliner `SW21 = ON_OFF`，`SW_ROCPU_SK-12D07-5_SPDT`） | [FILE] | 与本项目 ADR-0010（不设断电开关）相反 —— 但 nightliner 是**分体**，可能需要；不改我们的决策 |
| 9 | **SYSOFF 路线的 2N7002 补丁**（Conejo `Q1`、osprey `Q1`、designguide `Q2/Q4`，栅极网络 `100 Ω + 10 kΩ`） | [NET] | 本项目 `BQ24072` **没有 SYSOFF**（ADR-0010 已记），不需要；但**同一个 2N7002 在本项目被用于 RGB 门控的反相级**（ADR-0005 拓扑 C）——器件复用，值得在 BOM 里合并同料号 |

---

## 5. 对两个待决策项的净影响

### P13 充电电流档位 → **维持 `R_ISET = 1.78 kΩ`（0.5 A），但要说清这不是「和社区一致」**

- 社区 **4/4 全部选 USB500**，无一例走 ILIM 档换速度 ⇒ 输入档这一层我们与社区一致。
- ICHG 这一层**不可能一致**：社区按 0.5–1C 设计，而 3000 mAh 的 0.5–1C 是 1.5–3.0 A，
  撞在「芯片 1.5 A 上限 + USB500 的 500 mA 输入上限」两堵墙上。
- ⇒ 本项目的 0.5 A 是「**在社区一致认可的输入档下取满**」，这是一个**取舍**：
  选了 USB 规范合规与低发热，代价是 0.17C、约 6.2 h 充满。
- 若更看重速度并接受「在弱端口上可能不充」，可选 `power-architecture.md` §3.2 的方案 2（1.0 A）；
  那是**超出全部 4 个社区样本**的取值范围，由本项目自己承担风险。

### P14 温度保护 → **社区支持两条路，反对中间路线**

- 3/4 明确禁用（10 kΩ 到 GND）——与本项目现状一致，且这是 `[DS]` 认可的写法。
- 唯一的完整实现（nightliner）走的是 **3 脚电池座 + 电芯自带 NTC**（方案 B），
  **没有一例**把 NTC 焊在 PCB 上测板温（方案 C）——与 §3.3 的论证方向一致。
- ⇒ 若决定要保护，**照抄 nightliner 的 3 脚座做法**（把 `J2` 换成
  `Connector_JST:JST_XH_S3B-XH-A-1_1x03_P2.50mm_Horizontal` 或等效 3 脚座，
  中间脚命名 `BAT_TEMP` 接 `TS`），**并且采购的电芯必须带 3 芯引线**。
  这是一次同时改动「连接器选型 + BOM + 采购要求」的变更，不是改一颗电阻。

---

## 5.1 本次对照后**已经落地**到原理图的改动

| 改动 | 依据 |
| --- | --- |
| 新增 **`F1` = 500 mA 保险丝，装在 VBUS 侧**（`VBUS` → `F1` → `VCHG_IN` → `U1.IN`） | nightliner 的位置（Conejo 那颗在电池路径上，不可照抄） |
| `R_ILIM` **1.6 kΩ → 1.5 kΩ** | osprey / designguide 取值 |
| 新增 **`R_TMR` = 47 kΩ**（TMR 不再悬空） | 本项目自算：0.5 A × 3000 mAh 的 CC 段 ≈6.2 h > 默认 5 h；社区同值 |
| `U1` 封装改为 **`..._EP1.6x1.6mm_ThermalVias`** | nightliner 同做法；落实 `bq24072-pinout.md` §2.2 的 EP 热过孔要求 |
| `R_ISET` **保持 1.78 kΩ**（**未**照抄 3.9 kΩ） | 见 §3：3.9 kΩ 是对 200–500 mAh 电芯的 0.46–0.91C，照抄到 3000 mAh 会变成 0.077C |

**仍未采纳（各有原因）**：铁氧体磁珠 `FB1`（需先选型阻抗/额定电流，只 1 个先例）、
`TVS2200DRV`（只 1 个先例，且是 22 V 档器件，用于 5 V 输入需重新选型）、
`MAX17048` 电量计（3 个先例，但引入 I²C + 固件驱动，ZMK 支持情况未核实，且 GPIO 余量只剩 4）、
电池分压到 MCU ADC（1 个先例，nice!nano 已有内部方案）、
用 GPIO 控制 `R_ISET`（1 个先例，且会让 ISET 的电流监测失效，并结合 `[DS]` 的上电短路检测带来未知风险）。

---

## 6. 本报告不作为结论的项（诚实边界）

1. **样本量小**：真正可比的只有 4 个 BQ2407x 工程（社区主流根本不画充电电路）。
2. **[UNVERIFIED]** nightliner 的 `ILIM`/`TMR` 是否真的未装电阻 —— 提取器与源文件一致，
   但无法排除「装配另有版本」。**未据此判断该设计有缺陷。**
3. **[UNVERIFIED]** designguide 的 `J5`（Thermistor 连接器）与 `TS` 之间是否存在未画出的跳线。
4. **[UNVERIFIED]** `joric/nrfmicro` 用的具体充电 IC 型号（本报告未展开）。
5. **[UNVERIFIED]** 上述任何设计的**实物表现**（充电实测电流、是否误停充）——
   本报告全部是原理图/网表层面的**设计意图**，不是实测。
6. 社区样本的元件值取自**原理图属性**，与**实际 BOM / 贴装**可能不一致
   （Conejo 的 `RSET`/`RTMR` 就把值写成了占位字符串，可见这类字段在社区里并不可靠）。
7. **[UNVERIFIED]** 各项目的电池容量取自其 readme / 原理图图面文字（Conejo `300mAh`、
   osprey `250 mAh`、designguide 以 `500 mAh` 举例），nightliner **未标注** ——
   这是 §3 那张 C 倍率表的输入。若实际容量与标注不符，C 倍率结论会随之变化。

---

**结论一句话**：本项目被社区印证的，是**输入侧**的两个选择 ——
**USB500 档**（4/4）与 **`EN1` 接 `OUT` 轨**（4/4，无一例接 VBUS）；
温度监测上**跟着多数派禁用**（3/4），唯一做真温测的样本走的是「3 脚电池座 + 电芯 NTC」，
**没有任何样本用「板上 NTC」**。
但 **`R_ISET` 不能照抄**：社区的 0.23 A 是给 200–500 mAh 电芯的 0.5–0.9C，
按同样 C 率换算到 3000 mAh 需要 1.5–3 A，撞在 USB500 的 500 mA 输入上限上
⇒ 本项目维持 0.5 A（0.17C），这是**取舍而非对齐**。
本次对照**实际改掉了四处**（VBUS 侧保险丝、`R_ILIM` 1.5 kΩ、补装 `R_TMR` 47 kΩ、EP 热过孔封装），
其中 `R_TMR` 一条**修正了本项目原先「悬空即可」的错误结论**。
