DankFlumeMister/StarShield/research/large-battery-keyboard-charging-current.md

# 5000 mAh 以上键盘的充电电流：品牌官网 / 商品页 / 拆解实证

**调研日期**：2026-09-18
**触发**：用户「再联网搜索一下那些 5000mAh 以上电池的键盘是怎么处理充电电流的，
社区应该有很多案例才对，品牌键盘官网、GitHub 都找找」

**来源等级**：

| 标记 | 含义 |
| --- | --- |
| **[DOC]** | 厂商官方手册 / 官方商品页 / 评测网站**拆解实测**原文 |
| **[SRC]** | 直接读取仓库源文件（原理图 / 代码） |
| **[REPORTED]** | 媒体转述 |
| **[INFERENCE]** | 本报告推算 |

> **本报告修正了 `zmk-ecosystem-charging-precedent.md` 的样本偏差**：
> 那份报告的样本全是**小电池**（90–500 mAh）的 ZMK 开源板，据此得出「充电上限 350 mA」
> —— 这个结论**对 10000 mAh 场景不适用**。本文补齐了同容量段的商用产品。

---

## 1. 核心结论（先看这个）

1. **5000 mAh 以上的键盘确实存在，而且充电电流比小电池产品高得多**：
   实测区间 **350 mA … 1400 mA**。
2. ⭐ **换算成 C 率：0.035C – 0.163C**，本项目的 **0.049C 落在该区间的下三分之一**，
   与最保守的 Hola87（0.035C）接近。
3. ⭐ **拆解实证：商用无线键盘用 `TP4056`——线性充电芯片，最大 1 A**，
   **且实测用 2 线电池包（不带 NTC），尽管 TP4056 第 1 脚本身就支持 TEMP 温测**。
4. ⚠️ **它们普遍不遵守 USB 2.0 的 500 mA 限制**（取 1–1.4 A），代价是手册里必须写
   「勿用墙上充电器 / 快充头」这类警告。EPOMAKER、AULA、Kzzi 三家都有。
5. **又一次印证「双电芯并联 + 对称放置」**：Epomaker Galaxy100 Lite 的拆解确认
   内部是 **2 × 4000 mAh 对称布置**，用途之一正是平衡配重。

---

## 2. 样本总表（≥5000 mAh 为主，含对照）

| 产品 | 电池 | 充电电流 | 充满约 | 关背光电流 | 来源 |
| --- | --- | --- | --- | --- | --- |
| **AULA L99** | **8000 mAh** | **DC 5V ⚡ 1300 mA** | ≈6.2 h | ≤70 mA | [DOC] 官方手册 |
| **AULA F87S** | 10000 mAh（2×5000） | 未列 | — | — | [REPORTED] |
| **Kzzi Leop K98PRO** | 10000 mAh | **DC 5V / 1400 mA** | ≈7.1 h | 15 mA | [DOC] 官方手册 |
| **EPOMAKER TH87** | 10000 mAh | **≤1 A @5V**（手册警告上限） | ≈10 h | ≈50 mA | [DOC] 官方商品页 |
| **EPOMAKER Galaxy100 Lite** | **8000 mAh（2×4000）** | 未给数值；手册**严禁**墙上充电器 | — | ≈15.6 mA | [DOC] 评测（含拆解） |
| **Hola87** | 10000 mAh | **DC 5V / 350 mA** | ≈28.6 h | 14.3 mA | [DOC] 商品页规格 |
| 对照：Keychron K10 v2 | 4000 mAh | 5V / 1 A | ≈5 h | — | [DOC] 官方手册 |
| 对照：nRFMicro（ZMK 开源） | 90–300 mAh 级 | `RPROG` 外阻设定（原理图未填值） | — | — | [SRC] |
| 对照：Wireless Chameleon | 90–300 mAh | **50 / 150 mA**（焊桥选） | — | — | [DOC] 商品页 |
| 对照：mikoto（ZMK 开源） | 小电池 | **40/100/150/250/350 mA** | — | — | [SRC] 源码 |

**C 率换算** `[INFERENCE]`：

| 产品 | 充电电流 ÷ 容量 |
| --- | --- |
| AULA L99 | 1300 / 8000 = **0.163C** |
| Kzzi K98PRO | 1400 / 10000 = **0.140C** |
| EPOMAKER TH87 | ≤1000 / 10000 = **≤0.10C** |
| **本项目（当前）** | 485 / 10000 = **0.049C** |
| Hola87 | 350 / 10000 = **0.035C** |

⇒ **区间 0.035C – 0.163C；本项目的 0.049C 在**下三分之一**。**

---

## 3. ⭐ 拆解实证：商用键盘用的是 TP4056（线性，1 A）

一篇国内硬件社区的**整机拆解报告**（68 配列三模键盘，DURGOD/杜伽）给出了直接证据。**[DOC]**

| 拆解读出的结论（原文） | 含义 |
| --- | --- |
| 「充电芯片采用的是 **TP4056，线性充电芯片，最大支持 1A 充电电流**」 | **线性拓扑**，不是开关式；1 A 上限 |
| 「从电路图中可以看到 TP4056 **支持过温保护**，也就是第一脚 TEMP 的功能，**但是实际应用中采用了二线的电池包，并不是带有 NTC 特性的三线电池包**」 | ⭐ **即使 IC 支持，商用键盘也不用电池温度监测** |
| 电源管理另有 SOT23-5 的 DCDC；主控 NXP QN9080 | 说明「充电」与「系统供电」是分开的两套 |

**TP4056 的规格**（厂商页佐证）：ESOP-8 封装、可编程充电电流 **1000 mA**、
内置热调节、**C/10 充电终止**、**无充电安全定时器**。**[DOC]**

⇒ **两条重要含义：**

1. **「无定时器」在商用产品上再次得到印证** —— TP4056 同样没有，
   终止靠 C/10 判据。（与 nRFMicro 的 MCP73832/TP4054 一致。）
2. **「不用电池温度监测」也是商用常态** —— 拆解直接给出了因果：
   **IC 有 TEMP 脚，但厂商仍用 2 线电池包**。本项目的选择（10 kΩ 禁用）与之同向。

> ⚠️ **但散热条件不同**：TP4056 是 **ESOP-8**（封装面积大、可借键位区铜皮散热），
> 本项目的 BQ24072 是 **3 × 3 mm QFN**。数据手册的 `RθJA = 44.5 °C/W` 是
> **JEDEC 标准测试板**条件下的值；键盘 PCB 面积大、铺铜多，实际会显著更低，
> 但**不能直接照搬 TP4056 的 1 A 结论**。

---

## 4. 六个产品里五个都在「超 USB 规范」

| 产品 | 声明方式 | 实际输入电流 | 是否超 USB 2.0 的 500 mA |
| --- | --- | --- | --- |
| AULA L99 | 手册只写 5V/1300mA | 1300 mA | ✅ 超 **2.6 倍** |
| Kzzi K98PRO | 5.1 kΩ CC 下拉 + 手册 1.4 A | 1400 mA | ✅ 超 **2.8 倍** |
| EPOMAKER TH87 | 手册警告「勿用 >1A/5V 充电器」 | ≤1000 mA | ✅ 超 **2 倍** |
| EPOMAKER Galaxy100 Lite | 手册**严禁**墙上充电器 | 未给 | —（但严厉程度相同） |
| Hola87 | 350 mA | 350 mA | ❌ 唯一合规 |

**它们共同的免责话术**（三家原话，[DOC]）：
- 「建议**仅使用电脑 USB 接口**充电」
- 「**请勿使用快充手机充电器**」
- 「请勿使用劣质非标 / 过压过流电源适配器」

⇒ ⭐ 这说明**消费级键盘的通行做法是「按超过 CC 声明的电流设计，靠充电器宽容 + 免责声明兜底」**，
而不是「遵守规范」。

---

## 5. 对本项目 P13 的意义（修正此前的建议）

### 5.1 我上一轮的结论错在哪

上一轮我说「ZMK 生态充电上限仅 350 mA ⇒ 建议维持 0.5 A」。
**那个结论的样本选错了** —— ZMK 生态的开源无线板全是 **90–500 mAh** 的小电池设备
（分体键盘），它们的 350 mA 对应的是 **0.7–1C**，而不是「充电慢」。

⇒ 用它们来论证「10000 mAh 该用多大电流」是**把两个不同数量级混为一谈**。
本报告补齐同容量段证据后，图景变了：**同容量商用产品用 0.1–0.16C，我们只有 0.049C。**

### 5.2 三个可选档位（全部已核对 BQ24072 的约束）

| 档位 | 配置 | 充满 | C 率 | 对标 | 代价 |
| --- | --- | --- | --- | --- | --- |
| **维持 0.5 A** | `EN2=0/EN1=1`；R_ILIM 1.5 kΩ；R_ISET 1.78 kΩ | 20.6 h | 0.049C | Hola87（0.035C） | 无。**唯一完全符合 USB 声明** |
| **切 1.0 A** ⭐ | `EN2=1/EN1=0`；R_ILIM 1.6 kΩ；R_ISET **887 Ω** | ≈10 h | **0.10C** | **EPOMAKER TH87（≤1A）、Kzzi 的下半段** | 超 USB 声明 2 倍；耗散 1.3 W |
| 切 1.3 A | R_ILIM **1.24 kΩ**；R_ISET 887 Ω（充电仍 1 A，留 300 mA 余量给系统） | ≈10 h | 0.10C | AULA L99 的输入侧（1.3 A） | 超声明 2.6 倍；**输入侧压力最大** |

**BQ24072 在 1.0 A 档的约束核对** `[INFERENCE]`：

| 项 | 值 | 判定 |
| --- | --- | --- |
| 耗散 | (5 − 3.7) × 1.0 = **1.3 W** | — |
| `RθJA` = 44.5 °C/W（JEDEC 板） | 温升 ≈ **+58 °C** ⇒ `Tj` ≈ 83 °C（25 °C 环境）/ 98 °C（40 °C 密闭壳） | ✅ 低于 125 °C 热调节门限 |
| 实际 `RθJA` | 键盘 PCB 铺铜面积大，**必然低于** 44.5 °C/W | ✅ 更宽松（但未实测，见 §6） |
| 安全定时器 | 已接 VSS 禁用 | ✅ 不存在超时问题 |
| 输入不足时的行为 | `VIN-DPM` 自动降流 | ✅ 不会硬撑（这正是商用产品依赖的机制） |

⇒ **技术上 1.0 A 可行。** 它与 EPOMAKER TH87 的同容量做法一致，且 C 率落在商用区间中部。

### 5.3 建议

**证据不支持「0.5 A 是行业惯例」这个说法** —— 同容量段里只有 Hola87 一家这么保守。
但**支持「0.5 A 是唯一完全合规的选择」**。

⇒ 所以这仍是一次**取舍**，取决于你更看重哪一条：

- 看重**合规与最低发热** ⇒ 维持 **0.5 A**（20.6 h）
- 看重**与商用同容量产品对齐** ⇒ 切 **1.0 A**（≈10 h，0.1C，落在商用区间中部）

⚠️ **不建议 1.3 A 及以上**：那是拿输入侧的合规余量去换，而充电电流并没有变快
（R_ISET 决定充电电流，1.3 A 输入只是给了系统负载更多余量）。

---

## 6. 诚实边界

1. **各家的「充电电流」口径未必一致**：AULA/Kzzi 写的是「Charging Voltage/Current」，
   EPOMAKER 写的是「充电器电流上限」。**它们可能指输入电流而非电池充电电流**，
   而电池充电电流 ≤ 输入电流 ⇒ **本报告算出的 C 率是上界**。
2. **只有 1 台机器有拆解实证**（杜伽 68 键，2020 年设计），证明了 **TP4056 + 2 线电池包**。
   其余产品的充电 IC 型号**均未取得** —— Kzzi 的 1.4 A 与 AULA 的 1.3 A **都超过 TP4056 的 1 A 上限**，
   说明它们用了别的 IC（型号未知，可能是 IP2312 等开关式）。
   ⇒ **不能假定它们也是线性**，因此**它们的发热结论不能照搬到 BQ24072 上**。
3. **`RθJA = 44.5 °C/W` 是数据手册的 JEDEC 标准板条件**，本项目实际值**必须实测**
   （已在 §3.1 的 UNVERIFIED 列表里）。
   本报告 §5.2 的温升是**保守上界**，不是预测。
4. **未取得任何一款的官方原理图**：品牌键盘普遍不开源硬件（Keychron 亦然）。
   本报告的商用数据全部来自**手册/商品页/媒体拆解**，属二手。
5. **样本仍有限**（6 款 ≥5000 mAh + 拆解 1 台），**不是市场普查**；
   「区间 0.035–0.163C」是基于这些样本的描述，不代表全市场分布。
6. **未验证**：这些键盘在 USB 2.0 主机（严格限流 500 mA）下的实际充电表现
   —— 若它们真按 1.3 A 设计，插在严格限流的口上应当明显变慢，但无实测数据。
7. **GitHub 侧结论**：本轮搜索未发现任何**开源**的 5000 mAh+ 无线键盘硬件工程。
   开源无线键盘（ZMK 生态）几乎全是小电池分体键盘；大电池是**量产产品**的特征，
   而量产产品不开源。这是结构性事实，不是搜索不充分。
