DankFlumeMister/StarShield/research/keyboard-battery-capacity-precedent.md

# 商用无线键盘的电池容量与充电方案（10000 mAh 级）

**调研日期**：2026-09-17
**触发**：本项目电池容量决定改为 2×5000 mAh 并联（10000 mAh），需要核实
「市面 8000–10000 mAh 键盘是怎么做的」，特别是**它们如何绕过充电时间与安全定时器的矛盾**。

**来源等级**（全文遵守）：

| 标记 | 含义 |
| --- | --- |
| **[DOC]** | 厂商官方手册 / 官方商品页**原文**（第一手） |
| **[REPORTED]** | 媒体报道或第三方转述（**非**第一手，含转述损耗风险） |
| **[INFERENCE]** | 本报告基于上述数据的推算，**不是**厂商声明 |

⚠️ 本报告**不含实测**，全部为公开文档与推算。凡是推算都标了 `[INFERENCE]`。

---

## 1. 结论速览

1. **「2×5000 mAh 并联成 10000 mAh」是行业标准做法**，且官方理由与本项目独立推出的完全一致：
   单体 10000 mAh 软包**太厚**，塞不进扁平机身。**额外收益**是可把两块分置键盘左右两侧
   **平衡配重**。
2. ★ **消费级充电 IC 普遍没有「最长充电时间」限制** —— 本次调研最重要的发现。
   本报告最初是以**反推**得出的（Hola87 用 **350 mA** 充 **10000 mAh**，理论需 **28.6 h**；
   若其 IC 有 9.6 h 硬定时器则只能充到 1/3），当时标为 `[INFERENCE]`。
   ✅ **该推断已由后续调研升级为直接证据**（见 `research/zmk-ecosystem-charging-precedent.md`）：
   ZMK 官方推荐的开源板 **nRFMicro** 用 **MCP73832 / TP4054**，而 Microchip 官方规格明列
   `Charge Safety Timers: No` ⇒ **不再依赖反推**。
   **结论：BQ24072 的 `tMAXCHG` 是 TI 的额外高级特性，不是行业必需项。**
3. **商用充电电流没有统一答案**（350 mA … 2 A），但**普遍大于按 USB 规范可得的电流**。
   ⚠️ **措辞更正**：它们**并非「不做 CC 声明」** —— 用 Type-C 从充电器取电必须做 CC 下拉，
   否则端口不给电。准确说法是**按超出 5.1 kΩ 下拉所声明的 500 mA 的电流去设计**
   （超规范；实际能否取到取决于充电器是否严格限流）。代价就是手册里必须写
   「勿用快充充电器」「勿用劣质适配器」这类免责声明。
4. **「关背光」电流有两个独立样本交叉验证**：Kzzi 15 mA、Hola87 14.3 mA（推算）
   ⇒ 与本项目 `power-architecture.md` §5.2 的 5–15 mA 估算同量级。

---

## 2. 产品数据

### 2.1 AULA（狼蛛）F87S —— 最直接的对照样本

| 项 | 值 | 来源等级 |
| --- | --- | --- |
| 电池 | **10000 mAh，由 2 × 5000 mAh 并联而成** | [REPORTED] 官方承认，经 TechPowerUp 报道 |
| 官方给出的理由 | 单体 10000 mAh 锂电池**体积太大、厚度通常在 10 mm 以上**，很难塞进扁平机身 | [REPORTED] |
| 并联的额外好处 | 可**分散放置在键盘左右两侧**，「更好地平衡整把键盘的重量分布，不会一边重一边轻」 | [REPORTED] |
| 标称续航 | 关灯状态最高 **10000 小时** | [REPORTED] ⚠️ 数字存疑，见 §4 |
| 键盘类型 | 87 键，三模，8K 回报率，带 CNC 旋钮 | [REPORTED] |
| 价格 | 不到 90 美元 | [REPORTED] |

**同价位同类机型的电池容量（对照组）**：AULA F87 = 4000 mAh、Ajazz AK870 = 4000 mAh、
EPOMAKER F65 = 4000 mAh **[REPORTED]**。
⇒ 在**本报告的样本里**，**4000 mAh 是主流容量**（10000 mAh 属「堆料旗舰」定位）。
⚠️ 样本仅 4–5 个型号，**不足以代表全市场**。

⚠️ **电芯形态推断**：报道以「厚度」描述单体，故推断这些 5000 mAh 电芯是**软包（pouch）**
而非圆柱 —— 圆柱会以「直径」描述，且做到 5000 mAh 的圆柱是 21700（直径 **21 mm**，
远超键盘可容纳的厚度）。**[INFERENCE]**

### 2.2 Kzzi Leop K98PRO —— 10000 mAh + 大电流充电

| 项 | 值 | 来源等级 |
| --- | --- | --- |
| 键数 / 尺寸 / 重量 | 97 键 / 408.27 × 144.08 × 41.37 mm / 约 1260 g | [DOC] 官方手册 |
| 电池 | **10000 mAh** | [DOC] |
| **充电电压 / 电流** | **DC 5 V**（同页另有 `1.4 A` 字样，判定为充电电流） | [DOC] |
| ⇒ 充满时间 | **约 7.1 h** | [INFERENCE] 10000 mAh ÷ 1.4 A |
| 额定电流（默认灯效） | **≤ 180 mA @ 3.7 V** | [DOC] |
| 额定电流（关背光） | **≤ 15 mA** | [DOC] |
| 标称续航 | 约 55 h（默认灯效）/ 约 666 h（关背光） | [DOC] |
| 充电口 | Type-C | [DOC] |

**自洽性检验** `[INFERENCE]`：

- 180 mA × 55 h = **9900 mAh** ✅
- 15 mA × 666 h = **9990 mAh** ✅
⇒ 该手册的续航数字与容量、电流**三方自洽**，可信度高。

**官方充电警告（原文口径）**：建议**仅使用电脑 USB 接口**充电；**请勿使用快充手机充电器**；
请勿使用劣质非标电源适配器；请勿使用过压过流适配器。
⚠️ **注意其内在矛盾**：电脑 USB 口按规范只能给 500 mA（USB2.0）或 900 mA（USB3.0），
而它宣称 1.4 A ⇒ 实机上必然存在「插电脑口充得慢」的现象，厂商用免责声明处理。

### 2.3 Hola87 —— 10000 mAh + 极小电流充电（本次最关键的反证）

| 项 | 值 | 来源等级 |
| --- | --- | --- |
| 电池 | **10000 mAh，Lithium Electronic Battery** | [DOC] 商品页规格表 |
| **充电电流** | **DC 5 V / 350 mA** | [DOC] |
| ⇒ 充满时间 | **约 28.6 h** | [INFERENCE] 10000 mAh ÷ 0.35 A |
| 标称续航 | **79.68 h**（开背光）/ **700 h**（关背光） | [DOC] |
| RGB | 105 颗灯珠 | [DOC] |
| 布局 | 80% TKL，三模 | [DOC] |

**推算关背光电流**：10000 mAh ÷ 700 h = **14.3 mA** `[INFERENCE]`

⚠️ **这条数据是本报告的核心证据**：一台**在售商品**用 350 mA 充 10000 mAh（28.6 h）。
本项目的 BQ24072 若有 9.6 h 安全定时器，同容量下会永远只充到 1/3 —— 而这款产品显然没有这个问题。
⇒ **说明它的充电 IC 不存在「最长充电时间」约束。**

### 2.4 Keychron（对照：4000 mAh 主流档的充电电流）

| 型号 | 电池 | 充电电流 | 手册口径充电时间 | 来源等级 |
| --- | --- | --- | --- | --- |
| K10 v2 | 4000 mAh | 支持最高 **5V 1A** | 约 5 h | [DOC] 官方手册 |
| K10（老版） | 4000 mAh | 支持最高 **5V 2A** | 约 3 h | [DOC] 官方手册 |
| K8 | 4000 mAh | 支持最高 **5V 1A**（另有版本写 2A） | 约 3 h | [DOC] 官方手册 |

**交叉验证充电时间** `[INFERENCE]`：4000 mAh ÷ 1 A = 4 h（手册说 5 h）；
4000 mAh ÷ 2 A = 2 h（手册说 3 h）。两组都略大于纯 CC 推算值 ——
**这与「CV 段占最后约 30% 时间」的锂电充电特性一致**，
说明手册给的充电时间是含 CV 段的**实测口径**，可作参考。

⚠️ **Keychron 在手册里同时写了两组矛盾的说法**（K8：正文写 1A，脚注写 2A），
且都注明「支持最高 5V …」⇒ 说明它**不控制**输入电流，实际取决于充电器能给的量。
这也印证了 §1 结论 3。

---

## 3. 对本项目的直接影响

| # | 发现 | 对本项目的处置 |
| --- | --- | --- |
| 1 | 「2×5000 并联」是行业标准做法，理由是单体太厚 + 可平衡配重 | ✅ **采用**。本项目 95 键、外宽 379 mm，左右分置空间充足（原手工分件方案下更灵活） |
| 2 | 消费级充电 IC 普遍**没有**最长充电时间限制 | ✅ **`TMR` 接 VSS 禁用定时器**（数据手册明确支持）。这不是「拆掉保护」，而是**退回到全行业常规水平** |
| 3 | 商用充电电流 350 mA … 2 A 不等，普遍超 USB 规范 | ✅ 本项目**继续选 USB 合规路线**（5.1 kΩ `Rd` + USB500 档 = 0.5 A），代价是 20.6 h；快充路线与代价已量化在 `power-architecture.md` §3.5 |
| 4 | 两个独立样本的「关背光」电流为 **15 mA / 14.3 mA** | ✅ 反向印证 `power-architecture.md` §5.2 的 5–15 mA 估算合理，续航表（27–83 天）可引用 |
| 5 | 4000 mAh 是主流容量，10000 mAh 属旗舰堆料 | ℹ️ 本项目 10000 mAh 是**主动选择的旗舰指标**，需在教程里说明其对厚度/重量的代价 |

**仍然成立的三层保护（本项目与商用键盘都有）**：

1. 电芯自带保护板（过充 / 过放 / 过流）—— PCM
2. 充电 IC 的 4.2 V 恒压限制（`VBAT(REG)`）
3. 终止电流检测（`ITERM`，本项目 BQ24072 内部固定 0.1 × ICHG）

---

## 4. 诚实边界（本报告不作为结论的部分）

1. **样本只有 4 个品牌、5 个型号**，且是通过公开搜索可得的产品，**不是系统性市场普查**。
   不能据此声称「所有 10000 mAh 键盘都这么做」。
2. **AULA 的「2×5000 并联」是 [REPORTED] 而非 [DOC]**：官方承认 + 媒体转述，
   本项目**未取得**其规格书原文或拆解图。当作「行业普遍做法的旁证」，不作硬依据。
3. **AULA F87S 的「关灯续航 10000 小时」数字存疑**：按 10000 mAh 反推平均电流仅 **1 mA**，
   低于其同门 F87（4000 mAh）的合理量级，怀疑是「休眠态」而非「可用打字态」的口径。
   ⚠️ 本报告**不采用**该数字。
4. **Kzzi 的「1.4 A」判定有不确定性**：手册产品参数页「充电电压/电流」栏只印了 `DC 5V`，
   `1.4 A` 出现在紧随其后的充电说明区。本报告按充电电流理解并标注为 [DOC]，
   但该字段的**归属未经厂商确认** ⇒ 7.1 h 的推算相应不确定。
5. **所有充电电流与续航均为厂商标称**，非第三方实测。标称值通常对应理想条件
   （常温、特定亮度、新电芯）。
6. **未取得任何一款产品的原理图或充电 IC 型号**：因此「它们没有安全定时器」是
   **由充电时间反推的 [INFERENCE]**（Hola87 的 28.6 h > 任何 BQ24072 定时器上限），
   而非直接读到其 IC 的规格书。
   ⇒ 这条推断的**逻辑强度高但证据链不完整**，在 `power-architecture.md` §3.5 中已按此措辞表述。
7. 未调研：充电时键盘能否同时使用、边充边用的电流分配、是否支持 PD 快充协议等。

---

## 5. 检索记录

| 查询 | 有效来源 |
| --- | --- |
| `无线机械键盘 10000mAh 电池 充电 方案 18650 Type-C` | Kzzi K98PRO 手册（manualslib）、Newegg 商品页（Hola87 / Hola87 规格）、太平洋科技科普、数码之家 F87S 报道、PKNERGY 电芯供应商方案页 |
| `Keychron wireless mechanical keyboard battery 4000mAh charging current charging IC` | Keychron K10 v2 手册（manuals.plus）、K10 葡语手册、K8 手册（manuzoid / device.report） |
| `5000mAh 3.7V lithium polymer battery cell dimensions mm thickness 955465` | LiPol Battery 原厂 `LP955465` 规格（3 个独立域名同源），用于本项目电芯占位估算 |

⚠️ **未取得**：AULA 官方规格书、任何产品的充电 IC 型号、任何第三方拆解实测。
