DankFlumeMister/StarShield/docs/_tools/pcb_design.py

#!/usr/bin/env python3
# -*- coding: utf-8 -*-
"""pcb_design.py —— B4 PCB 布局的**单一真相源**（数据，不画图）

为什么单独拆这个文件（沿用 power_design.py / control_design.py 的既有做法）：
    `.kicad_pcb` 是**派生产物**。改布局只改本文件 + 跑 gen_pcb.py，
    再由 verify_pcb.py 断言。绝不要手工改 `Starshield.kicad_pcb`。

坐标约定（KiCad PCB 坐标，Y 向下为正）：
    板左上角 = (0, 0)。
    顶部 0..SHELF_H 是「控制肩」（方案 1：单板顶部加肩），放 28 个控制/电源件；
    其下才是键区（SHELF_H + BEZEL 起）。
    键区尺寸由 `docs/_generated/matrix.json` 实测推导，**不抄文档里的 371.5 mm**
    （那是按 19.50u 算的；实测 KLE 跨度是 19.25u = 366.71 mm，见 verify_pcb.py）。

⚠️ 关键实测来源（全部来自本仓库，不猜）：
  - 键区跨度：matrix.json 的 x_u ∈ [0.25, 19.50]，y_u ∈ [0, 6.25]
  - 轴体封装原点：自画 8 档 `SW_MX_Hotswap_Optional_*` 的 bbox 中心 = 原点 + (-2.54, +5.08)
    ⇒ **封装原点 = 轴体中心 + (2.54, -5.08)**
  - 灯珠偏移：参考板 apollo87h 实测 87/87 一致 = 轴体中心 + (0, +5.08)
  - 二极管偏移：参考板实测（多数）= 轴体中心 + (-8.33, +1.19)，旋 90°；
    本项目取 (-8.50, 0)，把「离轴体孔边 7.0 mm」的余量从 0.18 提到 0.35 mm
"""
import json
import os

U = 19.05           # 1u = 19.05 mm（MX 标准，与参考板实测行距交叉验证过）
BEZEL = 4.0         # G2 已定：键区四周留边 4 mm/边
SHELF_H = 24.0      # 方案 1：F 行上方加的控制肩高度（改这里即可切换方案）

# --- 键区（由 matrix.json 推导，勿手改）--------------------------------------
X_U_MIN, X_U_MAX = 0.25, 19.50
Y_U_MIN, Y_U_MAX = 0.0, 6.25
KEY_W = (X_U_MAX - X_U_MIN) * U        # 366.7125
KEY_H = (Y_U_MAX - Y_U_MIN) * U        # 119.0625
KEY_X0 = BEZEL                          # x_u = 0.25 处的板坐标
KEY_Y0 = SHELF_H + BEZEL                # y_u = 0    处的板坐标

BOARD_W = KEY_W + 2 * BEZEL             # 374.7125
BOARD_H = SHELF_H + KEY_H + 2 * BEZEL   # 151.0625

# --- 轴体封装原点相对轴体中心的偏移（8 档实测一致）----------------------------
SW_ORIGIN_DX = 2.54
SW_ORIGIN_DY = -5.08

# --- 二极管 / 灯珠 相对轴体中心的偏移与旋转（参考板实测）----------------------
DIODE_DX, DIODE_DY, DIODE_ROT = -8.50, 0.0, 90.0
LED_DX, LED_DY, LED_ROT = 0.0, 5.08, 0.0

# --- 安装孔（G3：8 个 / M2 自攻 / NPTH）---------------------------------------
# 全部落在「键区块」四周 2 mm 处，避开键区（孔边离键区 ≥0.9 mm），
# 且都在定位板轮廓内 ⇒ PCB 与定位板共用同一组孔位。
HOLE_FP = "MountingHole:MountingHole_2.2mm_M2"
_HOLE_INSET = 2.0
HOLES = [
    (f"H{i + 1}", round(x, 4), round(y, 4))
    for i, (x, y) in enumerate([
        (BOARD_W - _HOLE_INSET, _HOLE_INSET + SHELF_H * 0 + 60.0),   # 右 上
        (BOARD_W - _HOLE_INSET, 110.0),                              # 右 下
        (_HOLE_INSET, 60.0),                                         # 左 上
        (_HOLE_INSET, 110.0),                                        # 左 下
        (_HOLE_INSET, BOARD_H - _HOLE_INSET),                        # 底 左
        (BOARD_W * 1 / 3, BOARD_H - _HOLE_INSET),                    # 底 中左
        (BOARD_W * 2 / 3, BOARD_H - _HOLE_INSET),                    # 底 中右
        (BOARD_W - _HOLE_INSET, BOARD_H - _HOLE_INSET),              # 底 右
    ])
]

# --- 控制/电源 28 件在「控制肩」内的摆放 --------------------------------------
# 键区铺满、放不下（背面净空仅约 11 mm < 排针 18.78 mm），故走方案 1 的加肩。
# 排针旋转 90° 后长轴沿 X（31.48 × 3.54），两列相距 15.24 mm（Pro Micro 间距）。
# 值 = (x, y, rot)；全部 F.Cu。
CONTROL = {
    # nice!nano v2 排针（两条 1×13，2026-09-19 B6-1 由 1×12 修正）
    # ---- ⚠️ 2026-09-19 晚：方案①「口面与壳面齐平」重排（用户拍板）------------
    #   起因：插座原先在 (40, ·)，模块 USB 口面距板左边缘 **32.2 mm**
    #   ⇒ 侧壁开孔要 14×8 才放得过插头握持部，外观不像商业键盘。
    #   用户要求「像商业键盘一样，C 口与壳面齐平」。
    #   做法：**整组左移 30.46 mm** ⇒ 新孔1（= 模块最左那个孔）落在 x = 7.00，
    #   口面 = 7.00 − 5.30（实测孔1→口面）= **x = 1.70 mm** ⇒ 与壳内壁（≈0）几乎同平面。
    #   判据依据：口面距壳壁 < d2 − 握持部长（≈16 mm）时握持部才留在壳外
    #   （插头实测 d1=7 / d2=28 / w=13×7，见 docs/nice-nano-physical-verification.md §6.4）。
    #   ⚠️ 连带：`J1`（充电口）与 CC 下拉 / 保险丝 **让出左上角**，改到 x ≈ 155–170；
    #      模块天线端随之到 x ≈ 37–44（keepout 区，勿在下方放铜/件）。
    #   ⚠️ 新坐标**不改肩高（SHELF_H=24）与 y 向行距**，键区 / 定位板 / 板框一律不动。
    # ---- ⚠️ 2026-09-19 深夜（用户定稿）：左侧「接口簇」排布 -------------------
    #   用户要求：**模块口在左侧壁；充电口在左上角；开关紧挨充电口旁边**。
    #   空间核算（键区轴体从 y≈30.5 起，左侧壁可用段 ≈30 mm）：
    #     模块（板宽 17.78，两排插座相距 15.24）占 18 mm；
    #     J1（USB-C 母座，口朝 −Y）本体后缘 ≈ y 7.5；SW96 占 y ≈ 0–6.5。
    #     三者挤在同一角会重叠 ⇒ **把模块下移 5.78 mm**（两排 4.38/19.62 → **10.16/25.40**），
    #     让出 y 0–8 这一条给「充电口 + 开关」；模块后端 y≈26.7，距键区 30.5 仍有 3.8 mm 余量。
    #   ⇒ 左侧壁只有一个口（模块口，y ≈ 17.8）；左上角前壁两个口（充电 x=15、开关 x=33）。
    #   ⚠️ 开关 rot 仍为 180（柄朝 −Y 前壁），**档位左右顺序不变**（左→右 = 2.4G/蓝牙/有线）。
    "J3A": (9.54, 10.16, 90.0),
    "J3B": (9.54, 25.40, 90.0),
    # 三档模式开关（ADR-0009）
    # ---- 位置演进 ----
    #   (75,12) → (360,6)「右上角」→ (350,11)（用户反馈「太偏了」，往左下挪）
    #   → **(350,2.5, rot=180)**：用户 2026-09-19 说明「外壳开口开在侧面，和 USB-C 一个面」
    #     ⇒ 柄必须朝 −Y（后壁）且**够到板边**，详见下面的几何推算。
    # ---- 封装姿态（读 KiCad 官方 SW_SP3T_PCM13，实测非猜测）----
    #   本体 9.7 × 2.55 mm（沿 X 长）；4 个信号脚在 −Y 侧（y = −1.43）；
    #   **操作柄在 +Y 侧伸出行外**（本体面 y=1.6，柄尖到 F.CrtYd 的 y=3.4）
    #   ⇒ 这是「侧拨式」（Actuator Style: Side Slide），手指沿 X 方向推。
    # ---- 档位 ↔ 引脚的权威依据（C&K PCM 手册 SP3T 连接表）----
    #   手册原文：`SCHEMATIC SP3T  1-3  2-3  3-4`  ⇒ **pin3 = 公共端**（接 GND），
    #   **POS1→pin1、POS2→pin2、POS3→pin4**；封装焊盘 pin1/2/3/4 沿 X 依次在
    #   −3 / −1.5 / +1.5 / +3 mm ⇒ 三个档位在局部坐标自左向右为 POS1、POS2、POS3。
    # ⚠️ **rot=180 会镜像 X** ⇒ 板坐标自左(−X)向右(+X)变成 **POS3、POS2、POS1**；
    #   当前原理图 pin1=MODE0(有线)、pin2=MODE1(蓝牙)、pin4=MODE2(2.4G)
    #   ⇒ **左侧=2.4G(pos3/pin4)、中间=蓝牙(pos2/pin2)、右侧=有线(pos1/pin1)**，
    #   正好等于用户要的「从左往右：2.4G / 蓝牙 / 有线」。**改 rot 或改接线会反转顺序。**
    # ---- 为什么 y 只有 2.5（而不是用户先前说的「往下挪」）----
    #   侧壁开口要求**柄能穿过外壳侧壁**：柄尖在板坐标 y = y0 − 3.4。
    #   要让它探出板边(y=0)：y0 ≤ 3.4；探出 1 mm ⇒ y0 ≈ 2.4。
    #   ⇒ 取 y0 = 2.5（柄尖 y = −0.9，探出板边 0.9 mm）；
    #     最小的铜是机械焊盘 y = 2.5−1.43 = 1.07 mm，仍 ≥ 板边 0.5 mm 间距 ✓。
    #   ⚠️ 这一条与先前「往左下挪」的「下」冲突 —— 侧壁开口在物理上要求靠边。
    #     **2026-09-19 用户明确「不再向下挪」** ⇒ 定稿在 y = 2.5，不再回调；
    #     若日后外壳侧壁相对板边有外扩量 w，则取 y0 ≈ 3.4 − w。
    # ---- ⚠️ 2026-09-19 深夜：由「左上角」回到 **(33, 2.5, 180)** -------------
    #   用户要求「开关放在充电口旁边」⇒ 开关回到左上角，紧挨 J1（x=15）右侧。
    #   ⚠️ rot 仍为 180，柄朝 −Y（前壁）⇒ 档位自左向右 = 2.4G / 蓝牙 / 有线（与 ADR-0009 一致）。
    "SW96": (33.00, 2.50, 180.0),
    # 3 × 74HC595（ADR-0008 修订：3 颗才够 18 列）
    "U2": (95.00, 12.00, 0.0),
    "U3": (110.00, 12.00, 0.0),
    "U4": (125.00, 12.00, 0.0),
    "C4": (95.00, 20.50, 0.0),
    "C5": (110.00, 20.50, 0.0),
    "C6": (125.00, 20.50, 0.0),
    # 电源（BQ24072 充电 + 电池 + RGB 门控）
    # ⚠️ **2026-09-19 用户定：USB 充电口移到左上角**（原在 x=210 的顶肩中部）。
    #    y = 5.5：USB-C 的插口需要露出板边（壳体上沿开缺口），但**焊盘必须留在板内**
    #    （原取 4.8 时焊盘离板边仅 0.03 mm，DRC copper_edge_clearance 报 error 且会被切掉）。
    #    x = 15：顶肩最左端，避开左缘（焊盘要到 x ≥ 0.5）与 J3A（x ≥ 24.26）。
    # ⇒ **R1 / R2（USB-C 的 CC 下拉）与 F1 随之左移**，紧贴连接器：
    #    CC 走线必须短，否则属于 USB-C 的坏实践。U1 及其余电源件仍在原位（x 252+）。
    #    ⚠️ 代价：VBUS 从 F1（x≈18.5）到 U1（x=252）变成 ~230 mm 长线（0.8 mm 宽、1 A，电气无碍）。
    # ⚠️ **2026-09-19 晚（方案①）**：USB 充电口再次移位 —— 由左上角 → **x = 160**
    #    （595 链 x 91–135 与电源段 x 252+ 之间的空档）。
    #    原因：左上角让给 nice!nano 模块（其口面要贴左壁）。用户原「移到左上角」的
    #    意图在新的约束下改为「紧邻模块、仍偏左」；外壳上该口的开孔位置随之改到 x≈160。
    #    R1 / R2（CC 下拉）仍紧贴连接器（x 155/159，y=14）；F1 在 VBUS 侧（x=168）。
    #    ⚠️ 仍保持 y = 5.5：焊盘落在 y=1.46、本体探出板边约 1 mm（与原先同一套几何）。
    # ---- ⚠️ 2026-09-19 深夜：回到左上角（用户定稿「充电口在左上角」）---------
    #   与 J3A/J3B 的新排布配合：模块下移到两排 y = 10.16/25.40，让出 y 0–8；
    #   J1 本体后缘 ≈ y 7.5、外壳焊盘 y 6.55，与 J3A 插座本体（y 8.9–11.4）留 ~1.4 mm。
    #   R1/R2（CC 下拉）与 F1 仍紧贴 J1，放在两排插座之间的空档（y = 14，模块浮空在上方）。
    "J1": (15.00, 5.50, 0.0),      # USB-C：开口朝板外（−Y）= 前壁左上角
    "R1": (12.00, 14.00, 0.0),     # CC1 5.1k
    "R2": (16.00, 14.00, 0.0),     # CC2 5.1k
    "F1": (26.00, 14.00, 0.0),     # 2 A hold PTC（P15），在 VBUS 侧
    "U1": (252.00, 10.00, 0.0),    # BQ24072
    "C1": (260.00, 6.00, 0.0),
    "C2": (260.00, 14.00, 0.0),
    "C3": (268.00, 14.00, 0.0),
    "R3": (276.00, 6.00, 0.0),     # ILIM 1.6k
    "R4": (276.00, 14.00, 0.0),    # ISET 887
    "R5": (284.00, 6.00, 0.0),     # TS 10k（温测禁用）
    "R6": (284.00, 14.00, 0.0),    # 充电 LED 限流
    "D96": (292.00, 14.00, 0.0),   # 充电指示 LED
    "R7": (300.00, 6.00, 0.0),     # Q1 栅极上拉
    "R8": (300.00, 14.00, 0.0),    # Q2 栅极下拉
    "R9": (308.00, 6.00, 0.0),     # RGB_PWR_EN 串阻
    "Q1": (316.00, 6.00, 0.0),     # AO3401A（高边 P-MOS）
    "Q2": (316.00, 14.00, 0.0),    # 2N7002（反相级）
    "J2": (332.00, 10.00, 0.0),    # 电池座 JST-PH
}

# --- 定位板（G6：纳入第一版）--------------------------------------------------
# 与 PCB 同源：只覆盖键区（不含控制肩，否则 SP3T 开关与 USB-C 会被盖住），
# 外扩到与 PCB 同宽 ⇒ 与 PCB 共用同一组安装孔。
PLATE_X0, PLATE_Y0 = 0.0, SHELF_H
PLATE_W, PLATE_H = BOARD_W, BOARD_H - SHELF_H
PLATE_CUTOUT = 14.0    # MX 标准定位板开孔 14 × 14 mm

# --- 网络类（VLED 是唯一 2–3 A 路径，必须加宽）--------------------------------
# ⚠️ ADR-0007：RGB 由电池直供、不加升压 ⇒ VLED 是低阻抗大电流路径。
# ⚠️ 间距取值受「封装自身焊盘间隙」约束，实测（kicad-cli pcb drc）：
#    QFN-16 0.5mm 间距的焊盘间隙只有 0.229 mm、USB-C 座只有 0.200 mm
#    ⇒ 设 0.25 会让**封装自带**的间隙报 clearance error。故统一取 0.2（= 8 mil）。
NET_CLASSES = {
    "Default": dict(trace_width=0.25, via_diameter=0.6, via_drill=0.3, clearance=0.2),
    "VLED": dict(trace_width=2.0, via_diameter=1.2, via_drill=0.6, clearance=0.25),
    "Power": dict(trace_width=0.8, via_diameter=0.8, via_drill=0.4, clearance=0.2),
}
# 归属 Power 类的网（VLED 单独成类；GND 走铺铜）
POWER_NETS = {"OUT", "VBUS", "VCHG_IN", "VBAT"}


def load_matrix(root):
    """读 docs/_generated/matrix.json（几何唯一权威的派生数据）。"""
    p = os.path.join(root, "docs", "_generated", "matrix.json")
    with open(p, encoding="utf-8") as f:
        return json.load(f)


def key_center(e):
    """matrix.json 条目 → 轴体中心 (mm)。阶梯键的轴心固定在 centerX_u = 18.75u。"""
    cx = KEY_X0 + (e["centerX_u"] - X_U_MIN) * U
    cy = KEY_Y0 + (e["y_u"] + e["h_u"] / 2.0) * U
    return cx, cy


def switch_origin(e):
    """轴体封装的放置坐标（封装原点在引脚上，不在轴体中心）。"""
    cx, cy = key_center(e)
    return cx + SW_ORIGIN_DX, cy + SW_ORIGIN_DY
