DankFlumeMister/StarShield/docs/_tools/verify_firmware.py

#!/usr/bin/env python3
"""verify_firmware.py — 对 firmware/ 做静态校验

因为本机没有 Zephyr SDK（无法实跑 west build），本脚本用静态检查替代，
覆盖能在本地查证的项目：

  1. shield 文件齐套（对照 ZMK 官方 shield 的必需文件清单）
  2. build.yaml 语法与引用（board/shield 名、artifact-name）
  3. .conf 里每个 CONFIG_ 符号在 ZMK 官方 Kconfig 中存在；
     + Zephyr 侧「无 default y 必须手写」的驱动开关（如 WS2812_STRIP）是否漏写
  4. .keymap 每层绑定数 == 95，且与 transform 的位置数一致
  5. DTS 花括号/尖括号/圆括号配平（剥注释后）
  6. overlay 里引用的 phandle（&spi1/&spi3/&pro_micro/&shifter）都有定义
  7. 引脚不与保留脚冲突（P0.15 蓝灯 等）
  8. 90 颗 LED / 95 键等关键数字与文档一致
  9. C1 三档模式开关（toggle-mode + sideband + 3 GPIO + spi1 MISO 冲突修复）
 10. C3 软关机（CONFIG_ZMK_PM_SOFT_OFF + keymap 的 &soft_off 位置）与 USB boot
"""
import os
import re
import sys

try:
    sys.stdout.reconfigure(encoding="utf-8", errors="replace")
except Exception:
    pass

ROOT = os.path.dirname(os.path.dirname(os.path.dirname(os.path.abspath(__file__))))
SHIELD = os.path.join(ROOT, "firmware", "boards", "shields", "starshield")
ZMK = os.path.join(ROOT, "research", "_clones", "zmk")
FW = os.path.join(ROOT, "firmware")

fails = []
warns = []


def check(label, ok, detail="", warn=False):
    tag = "✅" if ok else ("⚠️ " if warn else "❌")
    print(f"  {tag} {label}" + (f"   {detail}" if detail else ""))
    if not ok and not warn:
        fails.append(label)
    if not ok and warn:
        warns.append(label)


def read(p):
    with open(p, encoding="utf-8") as f:
        return f.read()


# ── Zephyr 侧驱动开关表（3b 用）──────────────────────────────────
# compatible: (必须出现在 .conf 里的符号, 为什么必须手写)
# 这些符号定义在 Zephyr 而非 ZMK，ZMK 的 Kconfig 里查不到，且没有 default y，
# 也不依赖 devicetree 的 compatible —— 漏写不会编译失败，只在链接期报
# `undefined reference to __device_dts_ord_<N>'，极难定位（本项目 CI 第 4 次失败）。
ZEPHYR_DRIVER_CONFIG = {
    "worldsemi,ws2812-spi": (
        "WS2812_STRIP",
        "Zephyr menuconfig，无 default y；不开则 ws2812_spi.c 不编译 → 链接期 __device_dts_ord_N 未定义",
    ),
}
# 这些由 ZMK 的 Kconfig 依据 compatible 自动打开，【不该】写进 .conf。
# 反向查证 ZMK 源码确实有自动开关（两边都不写才是真错）。
ZMK_AUTO_DRIVER = {
    "zmk,gpio-595": ("app/module/drivers/gpio/Kconfig.595", "GPIO_595"),
}
ZEPHYR_OWNED = {sym for sym, _why in ZEPHYR_DRIVER_CONFIG.values()}


print("=" * 70)
print("1. shield 文件齐套")
print("=" * 70)
REQUIRED = [
    "starshield.zmk.yml", "Kconfig.shield", "Kconfig.defconfig",
    "starshield.overlay", "starshield.keymap", "starshield.conf",
    "starshield_transform.dtsi",
]
for f in REQUIRED:
    check(f, os.path.exists(os.path.join(SHIELD, f)))

print()
print("=" * 70)
print("2. build.yaml")
print("=" * 70)
try:
    import yaml
    b = yaml.safe_load(read(os.path.join(FW, "build.yaml")))
    inc = b.get("include", []) if isinstance(b, dict) else []
    check("YAML 可解析", True, f"{len(inc)} 个构建项")
    names = []
    for it in inc:
        board = it.get("board", "")
        shield = it.get("shield", "")
        art = it.get("artifact-name")
        check(f"  项 board={board} shield={shield}", bool(board) and bool(shield))
        names.append(art or f"{shield}-{board.replace('/', '_')}-zmk")
    check("artifact-name 互不重复", len(names) == len(set(names)), ", ".join(names))
except ImportError:
    check("PyYAML 可用", False, "未安装 pyyaml，跳过 build.yaml 解析", warn=True)
except Exception as e:
    check("build.yaml 可解析", False, str(e)[:80])

print()
print("=" * 70)
print("3. .conf 里的 CONFIG 符号是否真实存在于 ZMK")
print("=" * 70)
kconfig_text = ""
for dirpath, _dirs, files in os.walk(ZMK):
    for fn in files:
        if fn.startswith("Kconfig"):
            try:
                kconfig_text += read(os.path.join(dirpath, fn)) + "\n"
            except Exception:
                pass
defined = set(re.findall(r'^\s*(?:menu)?config\s+([A-Z0-9_]+)', kconfig_text, re.M))
check("已加载 ZMK Kconfig", len(defined) > 300, f"{len(defined)} 个符号")

conf = read(os.path.join(SHIELD, "starshield.conf"))
used = re.findall(r'^(CONFIG_[A-Z0-9_]+)=', conf, re.M)
# 下面这些符号属于 Zephyr 而非 ZMK，在本机（无 Zephyr 源码）查不到，
# 交给 3b 按 devicetree compatible 反查，见文件顶部 ZEPHYR_DRIVER_CONFIG 的说明。
for sym in used:
    bare = sym[len("CONFIG_"):]
    if bare in ZEPHYR_OWNED:
        check(f"  {sym}", True, "Zephyr 符号，由 3b 按 compatible 校验")
        continue
    check(f"  {sym}", bare in defined, "" if bare in defined else "ZMK Kconfig 中不存在")

print()
print("=" * 70)
print("3b. Zephyr 侧驱动开关：该手写的有没有漏写")
print("=" * 70)
# ⚠️ 上面的 3 只检查「符号在 ZMK Kconfig 里存在」，覆盖不到 Zephyr 原生驱动开关。
#    曾经的翻车（CI 第 4 次失败）：overlay 里写了 worldsemi,ws2812-spi，
#    CONFIG_ZMK_RGB_UNDERGLOW=y 也开了，但没写 CONFIG_WS2812_STRIP=y。
#    ZMK 的 underglow 只 select LED_STRIP（上层 API），底层驱动开关是 Zephyr 的
#    menuconfig WS2812_STRIP —— 它没有 default y、也不看 devicetree 的 compatible，
#    结果 ws2812_spi.c 根本没进编译，设备结构体没生成，链接期才炸：
#    undefined reference to `__device_dts_ord_129'。
#    注意与 ZMK 自己的 595 驱动对比：Kconfig.595 写了
#    `default $(dt_compat_enabled,$(DT_COMPAT_ZMK_GPIO_595))`，所以它是自动开的。
#    两者行为不同 —— 下面把「必须手写」和「会自动开」分开断言。
ov_text = read(os.path.join(SHIELD, "starshield.overlay"))
for compat, (sym, why) in ZEPHYR_DRIVER_CONFIG.items():
    if compat not in ov_text:
        continue
    check(f"  {compat} → .conf 里有 CONFIG_{sym}=y",
          re.search(rf'^CONFIG_{sym}=y\s*$', conf, re.M) is not None,
          why)
for compat, (rel, sym) in ZMK_AUTO_DRIVER.items():
    if compat not in ov_text:
        continue
    kc = read(os.path.join(ZMK, rel))
    check(f"  {compat} → ZMK 自动开启 {sym}",
          "default $(dt_compat_enabled" in kc,
          "ZMK 源码里应有 default $(dt_compat_enabled,...)，否则该驱动永远不编译")

print()
print("=" * 70)
print("4. keymap 每层绑定数 == 95")
print("=" * 70)
km = read(os.path.join(SHIELD, "starshield.keymap"))
km_nc = re.sub(r"/\*.*?\*/", " ", km, flags=re.S)
for layer in ["default_layer", "fn_layer"]:
    m = re.search(layer + r"\s*\{(.*?)bindings\s*=\s*<(.*?)>;", km_nc, re.S)
    if not m:
        check(f"{layer} 找到", False)
        continue
    binds = re.findall(r"&\w+", m.group(2))
    check(f"  {layer} 绑定数 = {len(binds)}", len(binds) == 95)

tf = read(os.path.join(SHIELD, "starshield_transform.dtsi"))
tf_nc = re.sub(r"/\*.*?\*/", " ", tf, flags=re.S)
mapm = re.search(r"map\s*=\s*<(.*?)>;", tf_nc, re.S)
rc = re.findall(r"RC\(\s*(\d+),\s*(\d+)\)", mapm.group(1)) if mapm else []
check(f"transform 条目数 = {len(rc)}", len(rc) == 95)
cells = set((int(a), int(b)) for a, b in rc)
check(f"transform 矩阵格唯一 = {len(cells)}", len(cells) == 95, "无冲突")

print()
print("=" * 70)
print("5. DTS 括号配平（剥注释）")
print("=" * 70)
# 注意：像键盘那样键帽标签里带括号（如 `(/9` `)/0`）时，注释剥除必须换成空格占位，
# 否则注释内的括号会被误算。这里用等长空格替换，保持行结构。
for f in ["starshield.overlay", "starshield_transform.dtsi"]:
    t = read(os.path.join(SHIELD, f))
    body = re.sub(r"/\*.*?\*/", lambda m: " " * len(m.group(0)), t, flags=re.S)
    body = re.sub(r"//[^\n]*", "", body)
    cb = body.count("{") - body.count("}")
    ab = body.count("<") - body.count(">")
    pb = body.count("(") - body.count(")")
    detail = f"{{}}={cb} <>={ab} ()={pb}"
    check(f"  {f}  {detail}", cb == 0 and ab == 0 and pb == 0)
    if pb != 0:
        for i, l in enumerate(body.splitlines(), 1):
            if l.count("(") != l.count(")"):
                print(f"        L{i}: {l.strip()[:100]}")

print()
print("=" * 70)
print("6. overlay 引用的 phandle 是否有定义")
print("=" * 70)
ov = read(os.path.join(SHIELD, "starshield.overlay"))
ov_nc = re.sub(r"/\*.*?\*/", lambda m: " " * len(m.group(0)), ov, flags=re.S)
# 本文件 + 其本地 include 一起算作「已定义」
combined = ov_nc
for inc in re.findall(r'#include\s+"([^"]+)"', ov_nc):
    p = os.path.join(SHIELD, inc)
    if os.path.exists(p):
        sub = read(p)
        combined += "\n" + re.sub(r"/\*.*?\*/", lambda m: " " * len(m.group(0)), sub, flags=re.S)
refs = set(re.findall(r"&([a-z_][a-z0-9_]*)", combined))
labels = set(re.findall(r"^\s*([a-z_][a-z0-9_]*)\s*:", combined, re.M))
overrides = set(re.findall(r"^\s*&([a-z_][a-z0-9_]*)\s*\{", combined, re.M))
BOARD = {"spi1", "spi3", "pinctrl", "pro_micro", "gpio0", "gpio1", "adc",
         "gpiote", "usbd", "flash0", "reg0", "reg1", "key_physical_attrs",
         # ZMK 上游 behaviors.dtsi 定义的内置行为（本 shield 的 C1 档位绑定会引用它们）
         "bt", "out"}
check("physical_layout0 已定义", "physical_layout0" in labels)
check("default_transform 已定义", "default_transform" in labels)
for r in sorted(refs):
    ok = (r in labels) or (r in overrides) or (r in BOARD)
    check(f"  &{r}", ok, "" if ok else "既非本 shield 定义，也不在板级白名单")

print()
print("=" * 70)
print("7. 关键数字与引脚安全")
print("=" * 70)
check("chain-length = 95（LED 数）", "chain-length = <95>" in ov)
check("ngpios = 24（3 颗 595 级联；2026-09-18 修订，原 2 颗驱动不了 18 列）", "ngpios = <24>" in ov)
check("diode-direction = col2row", 'diode-direction = "col2row"' in ov)
check("列数 18", len(re.findall(r"<&shifter\s+\d+", ov)) == 18,
      f"实得 {len(re.findall(r'<&shifter', ov))}")
m_rows = re.search(r"row-gpios([\s\S]*?);", ov)
check("行数 6", m_rows is not None and len(re.findall(r"<&pro_micro\s+\d+\s+\(", m_rows.group(0))) == 6,
      f"实得 {len(re.findall(r'<&pro_micro', m_rows.group(0))) if m_rows else '?'}")
check("EXT_POWER 节点名正确", "EXT_POWER {" in ov, "ZMK 要求此名以保留用户设置")
check("未占用 P0.15（蓝灯）", "0 15" not in ov)
check("未占用 P0.13（VCC 门控）", "0 13" not in ov)

print()
print("=" * 70)
print("8. 595 与 WS2812 使用不同 SPI 外设（否则两个从设备冲突）")
print("=" * 70)
spi595 = "&spi1" in ov
spi_rgb = "&spi3" in ov
check("595 在 &spi1 且 RGB 在 &spi3", spi595 and spi_rgb, f"spi1={spi595} spi3={spi_rgb}")

print()
print("=" * 70)
print("9. C1 三档模式开关（ADR-0009 + B2 的 GPIO 定案 D2/D14/D18）")
print("=" * 70)
# ---- kscan toggle 节点 ----
m_tog = re.search(r"kscan_sp3t_toggle:\s*kscan_sp3t_toggle\s*\{([\s\S]*?)\n    \};", ov)
check("存在 kscan_sp3t_toggle 节点", m_tog is not None)
if m_tog:
    body = m_tog.group(1)
    check('compatible = "zmk,kscan-gpio-direct"',
          'compatible = "zmk,kscan-gpio-direct";' in body)
    check("toggle-mode 已打开", "toggle-mode;" in body)
    check("wakeup-source（拨动开关可唤醒深睡，Altar I 同款）",
          "wakeup-source" in body)
    gpios = re.findall(r"<&pro_micro\s+(\d+)\s+([^>]+)>", body)
    check("恰好 3 个输入脚，且是 D2 / D14 / D18（B2 定案 MODE0/1/2）",
          [g[0] for g in gpios] == ["2", "14", "18"], str([g[0] for g in gpios]))
    check("三档全部 GPIO_ACTIVE_LOW（公共端接 GND，原理图 SW96）",
          all("GPIO_ACTIVE_LOW" in g[1] for g in gpios))
    check("DT 里【不写】pull 标志（驱动按极性自行推导，ADR-0009 核对过驱动源码）",
          all("PULL_" not in g[1] for g in gpios))

# ---- sideband 映射 ----
m_sb = re.search(r"endpoint_sideband_behaviors\s*\{([\s\S]*?)\n    \};", ov)
check("存在 endpoint_sideband_behaviors 节点（sideband 写法，与 keymap 解耦）", m_sb is not None)
if m_sb:
    sb = m_sb.group(1)
    check('compatible = "zmk,kscan-sideband-behaviors"',
          'compatible = "zmk,kscan-sideband-behaviors";' in sb)
    check("auto-enable", "auto-enable;" in sb)
    check("kscan 指向 kscan_sp3t_toggle", "kscan = <&kscan_sp3t_toggle>;" in sb)
    cols = re.findall(r"column = <(\d)>;\s*\n\s*bindings = <([^>]+)>;", sb)
    check("三档列序 = 0/1/2", [c[0] for c in cols] == ["0", "1", "2"], str([c[0] for c in cols]))
    check("档 0（有线）= &out OUT_USB", cols and cols[0][1] == "&out OUT_USB",
          str(cols[0][1] if cols else "?"))
    check("档 1（蓝牙）经宏 → OUT_BLE + 配对位 0", cols and cols[1][1] == "&mode_ble_host",
          str(cols[1][1] if cols else "?"))
    check("档 2（2.4G）经宏 → OUT_BLE + 配对位 1", cols and cols[2][1] == "&mode_dongle",
          str(cols[2][1] if cols else "?"))

# ---- 档位宏 ----
m_ble = re.search(r"mode_ble_host:\s*mode_ble_host\s*\{([\s\S]*?)\n        \};", ov)
m_dgl = re.search(r"mode_dongle:\s*mode_dongle\s*\{([\s\S]*?)\n        \};", ov)
check("宏 mode_ble_host = OUT_BLE + BT_SEL 0（直连主机）",
      m_ble is not None and "&out OUT_BLE &bt BT_SEL 0" in m_ble.group(1))
check("宏 mode_dongle = OUT_BLE + BT_SEL 1（连 Dongle，ADR-0001）",
      m_dgl is not None and "&out OUT_BLE &bt BT_SEL 1" in m_dgl.group(1))

# ---- spi1 MISO 冲突（🔴 本次 C1 实测发现并修复）----
p_ov = os.path.join(SHIELD, "starshield.overlay")
m_pc = re.search(r"&pinctrl\s*\{([\s\S]*?)\n\};", ov)
check("覆盖了板级 spi1 pinctrl（nice!nano 默认把 MISO 放在 P1.11 = D14，与 MODE1 冲突）",
      m_pc is not None and "spi1_default" in (m_pc.group(1) if m_pc else ""))
if m_pc:
    pc = m_pc.group(1)
    check("spi1 只保留 SCK(P1.13) + MOSI(P0.10)（595 是只写器件，不需要 MISO）",
          "SPIM_SCK, 1, 13" in pc and "SPIM_MOSI, 0, 10" in pc and "SPIM_MISO" not in pc)

print()
print("=" * 70)
print("10. C3 软关机 + USB boot（配合 ADR-0010 不设物理断电开关）")
print("=" * 70)
conf = read(os.path.join(SHIELD, "starshield.conf"))
check("CONFIG_ZMK_PM_SOFT_OFF=y 已开", "CONFIG_ZMK_PM_SOFT_OFF=y" in conf)
check("CONFIG_ZMK_USB_BOOT=y 已开", "CONFIG_ZMK_USB_BOOT=y" in conf)

km = read(os.path.join(SHIELD, "starshield.keymap"))
check("keymap 引用 &soft_off 恰好一次（避免误触/重复绑定）", km.count("&soft_off") == 1,
      f"出现 {km.count('&soft_off')} 次")
m_fn = re.search(r"fn_layer\s*\{[\s\S]*?bindings = <([\s\S]*?)>;", km)
if m_fn:
    binds = re.findall(r"&[A-Za-z_][A-Za-z0-9_]*(?:\s+[A-Za-z_0-9]+)*", m_fn.group(1))
    binds = [b.strip() for b in binds]
    idx = [i for i, b in enumerate(binds) if b.startswith("&soft_off")]
    check("&soft_off 在 FN 层位置 16（小键盘 `/`；换位置要同步本断言与 .conf 注释）",
          idx == [16], f"实际位置 {idx}")
check("base 层不含 &soft_off（软关机不应在日常层裸绑）",
      "default_layer" in km and "&soft_off" not in
      re.search(r"default_layer\s*\{[\s\S]*?bindings = <([\s\S]*?)>;", km).group(1))

print()
print("=" * 70)
if fails:
    print(f"结论：❌ 未通过（{len(fails)} 项失败）")
    for f in fails:
        print("   -", f)
    if warns:
        print(f"（另有 {len(warns)} 项警告）")
    sys.exit(1)
print("结论：✅ 全部静态校验通过")
if warns:
    print(f"（{len(warns)} 项警告，见上）")
sys.exit(0)
